ryule5158/A-Rack-for-Eurorack-Modules/exports/Rack4Modules_DesktopTilt60_V04_05_Isometric.png

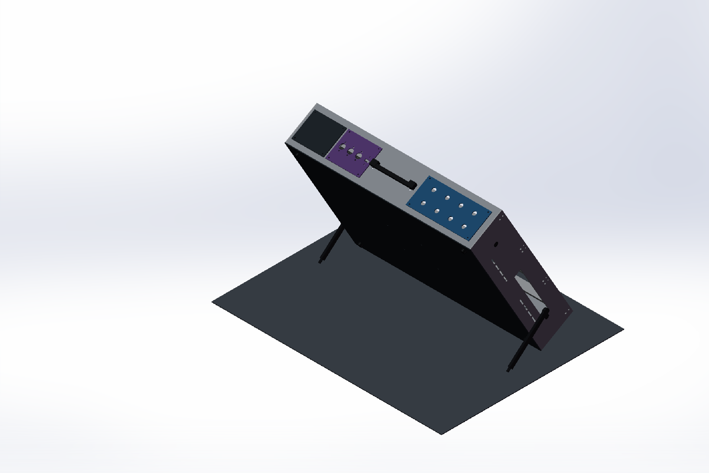
exports/Rack4Modules_DesktopTilt60_V04_05_Isometric.png
