ryule5158/A-Rack-for-Eurorack-Modules/exports/Rack4Modules_OpenCase_V04_01_ModuleFront.png

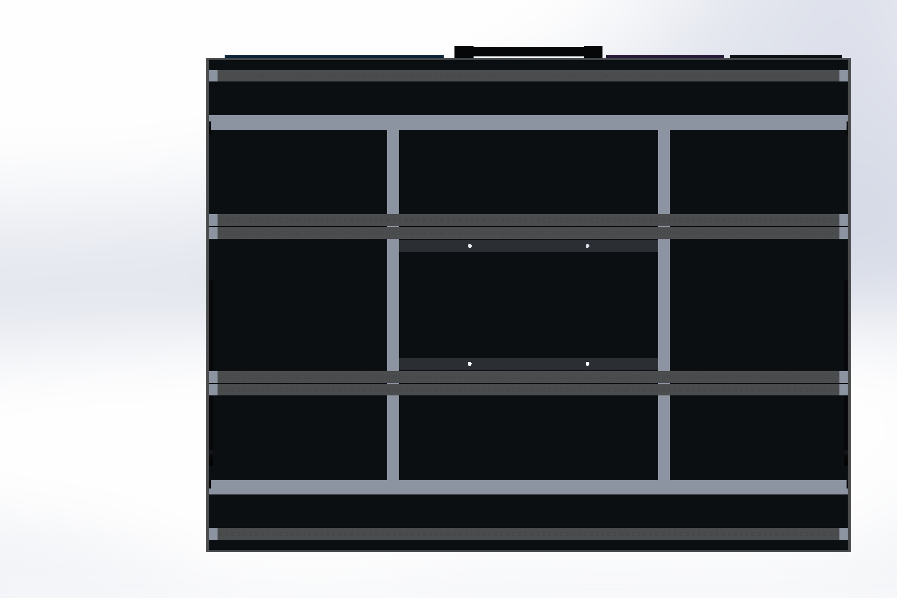
exports/Rack4Modules_OpenCase_V04_01_ModuleFront.png
