ryule5158/A-Rack-for-Eurorack-Modules/exports/Rack4Modules_OpenCase_V04_02_Isometric.png

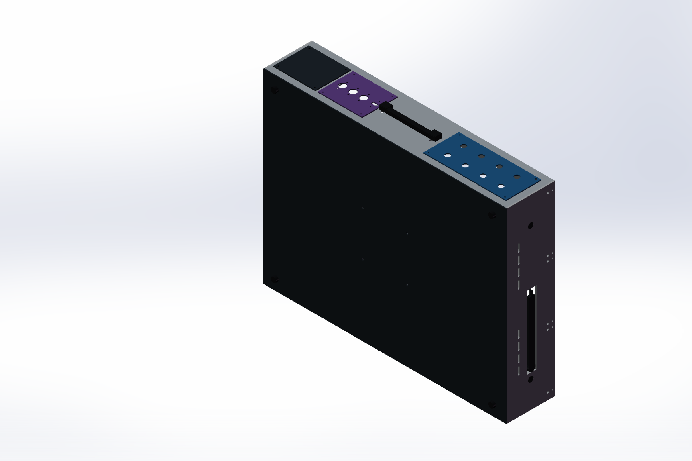
exports/Rack4Modules_OpenCase_V04_02_Isometric.png
