ryule5158/A-Rack-for-Eurorack-Modules/exports/Rack4Modules_OpenCase_V04_03_UpperEdge_IO.png

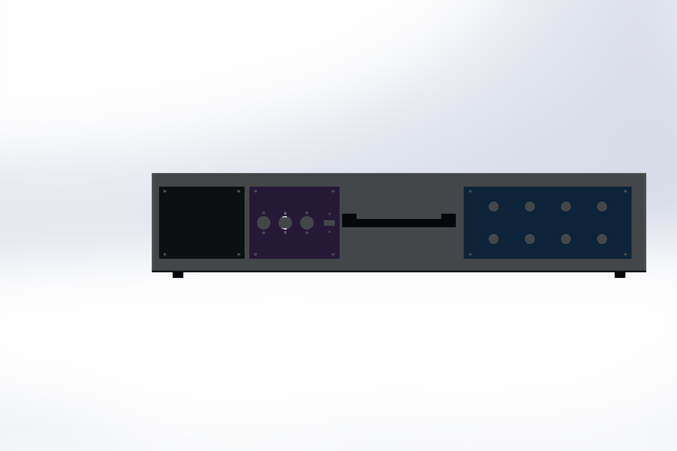
exports/Rack4Modules_OpenCase_V04_03_UpperEdge_IO.png
