ryule5158/A-Rack-for-Eurorack-Modules/previews/Rack4Modules_DesktopTilt60_07_Isometric_V07.png

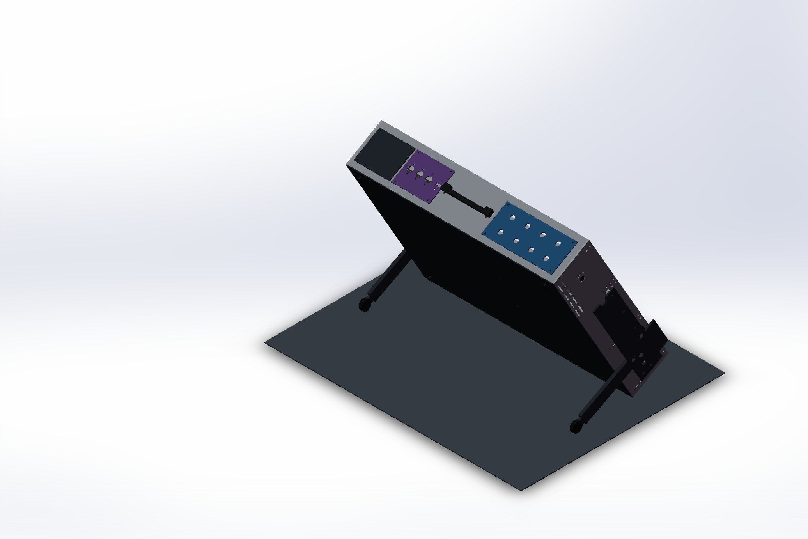
previews/Rack4Modules_DesktopTilt60_07_Isometric_V07.png
