ryule5158/A-Rack-for-Eurorack-Modules/previews/Rack4Modules_ShowcaseTilt60_LidOff_01_Isometric_V07.png

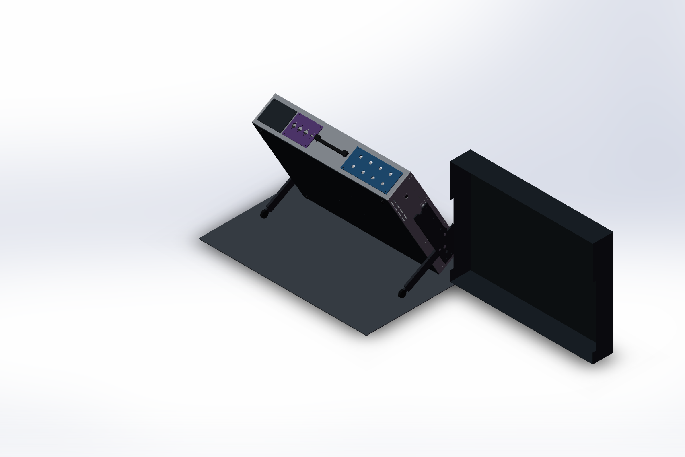
previews/Rack4Modules_ShowcaseTilt60_LidOff_01_Isometric_V07.png
