ryule5158/A-Rack-for-Eurorack-Modules/previews/Rack4Modules_TransportClosed_06_RightSide_V07.png

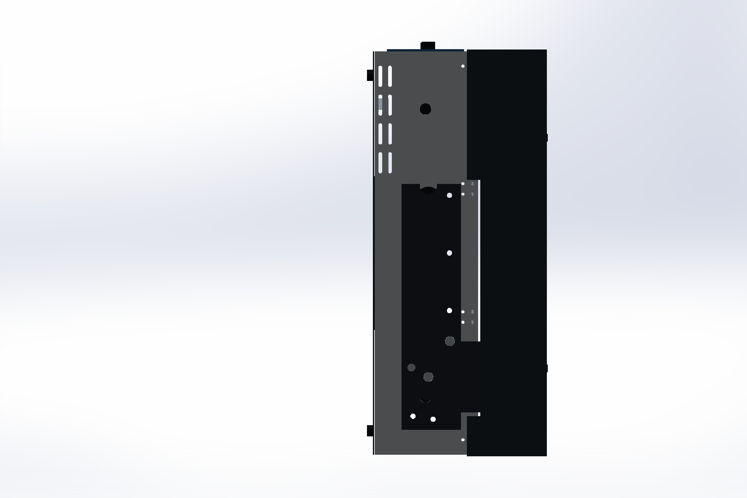
previews/Rack4Modules_TransportClosed_06_RightSide_V07.png
