ryule5158/A-Rack-for-Eurorack-Modules/exports/StandOuterCheek_V11_4mm_FullPlate.STEP

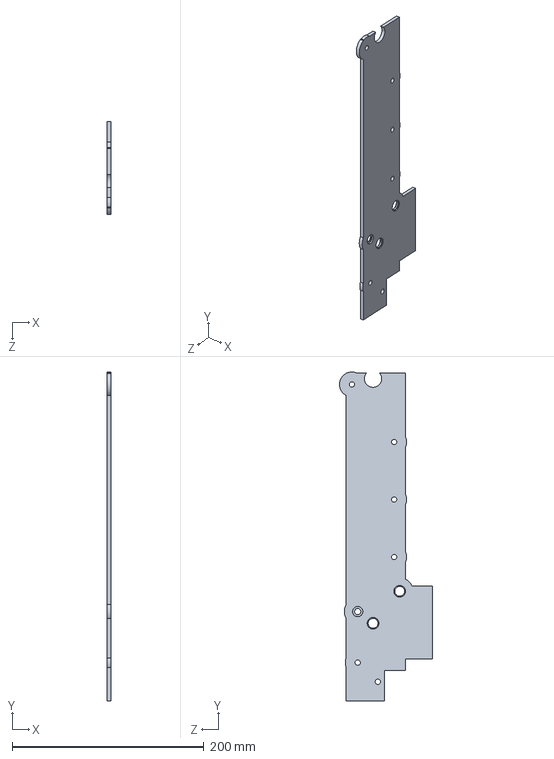
[picture p13: CAD file, 2026-08-29]
exports/StandOuterCheek_V11_4mm_FullPlate.STEP
4.00 x 343.0 x 97.0 mm
