ryule5158/A-Rack-for-Eurorack-Modules/cad/parts/DeepTravelLid_V08_Rymovia_StandRelief.SLDPRT

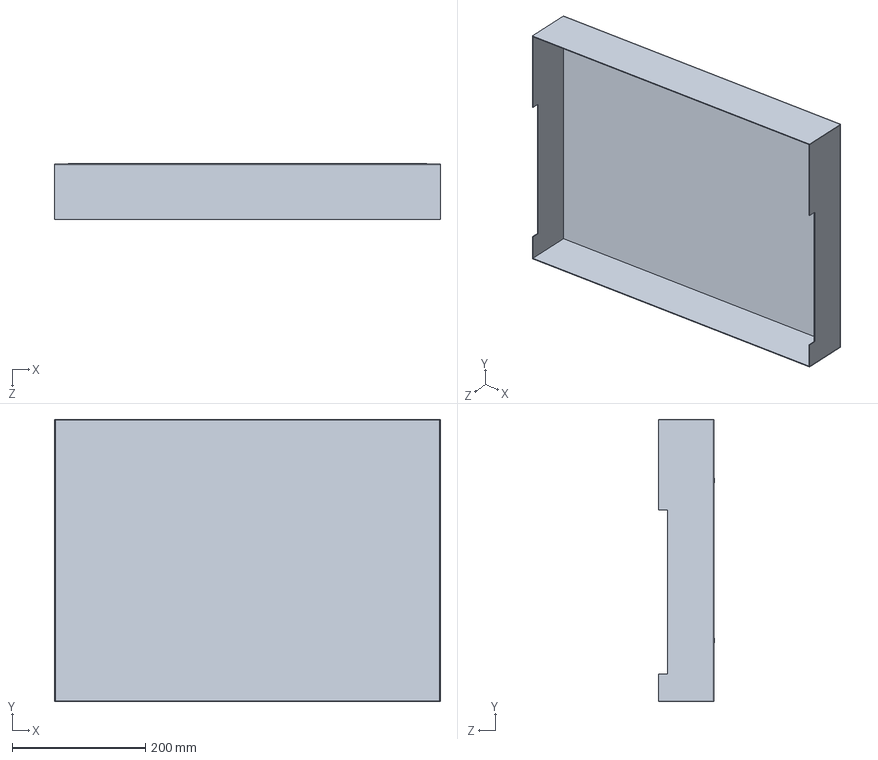
[picture p14: CAD file, 2026-08-26]
cad/parts/DeepTravelLid_V08_Rymovia_StandRelief.SLDPRT
579.0 x 423.4 x 84.4 mm
