ryule5158/A-Rack-for-Eurorack-Modules/exports/RearKickstandHeelPin_V11_M4.STEP

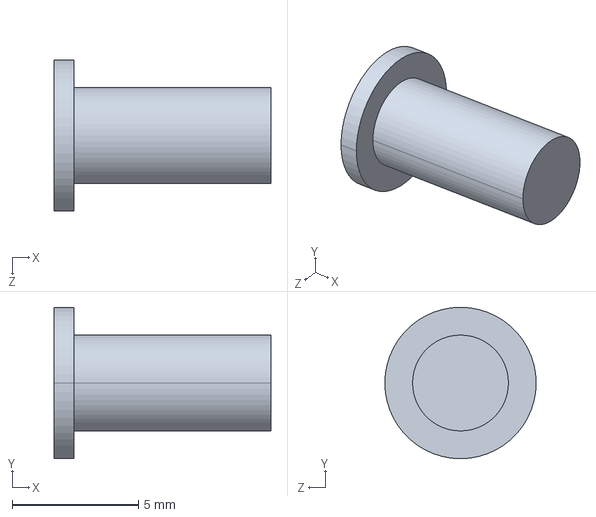
[picture p15: CAD file, 2026-08-29]
exports/RearKickstandHeelPin_V11_M4.STEP
8.60 x 6.00 x 6.00 mm
