ryule5158/A-Rack-for-Eurorack-Modules/cad/parts/RailEndBlock_M3.SLDPRT

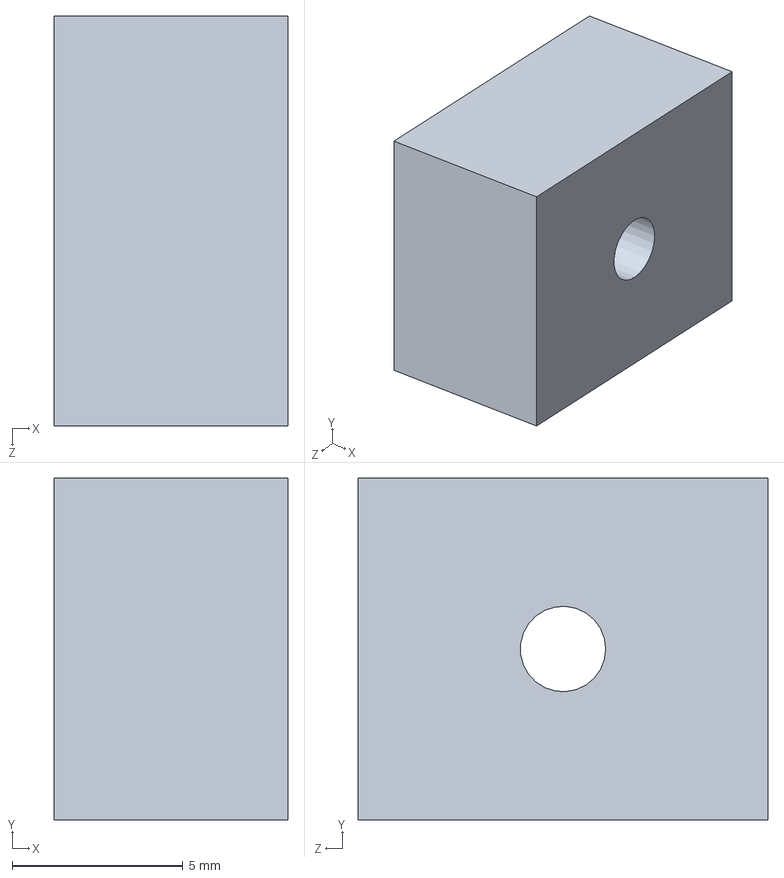
[picture p16: CAD file, 2026-08-26]
cad/parts/RailEndBlock_M3.SLDPRT
6.84 x 10.0 x 12.0 mm
