ryule5158/A-Rack-for-Eurorack-Modules/cad/parts/SideRecessedLeg_V03_TwoPosition.SLDPRT

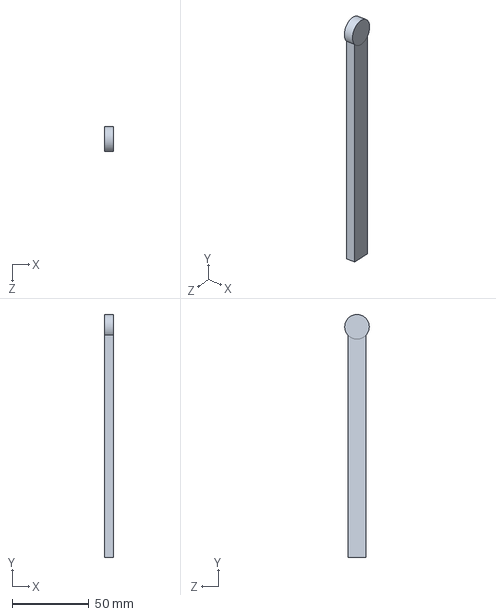
[picture p18: CAD file, 2026-08-26]
cad/parts/SideRecessedLeg_V03_TwoPosition.SLDPRT
6.00 x 158.0 x 16.0 mm
