ryule5158/A-Rack-for-Eurorack-Modules/exports/StandCheekFastenerPack_V11_M5.STEP

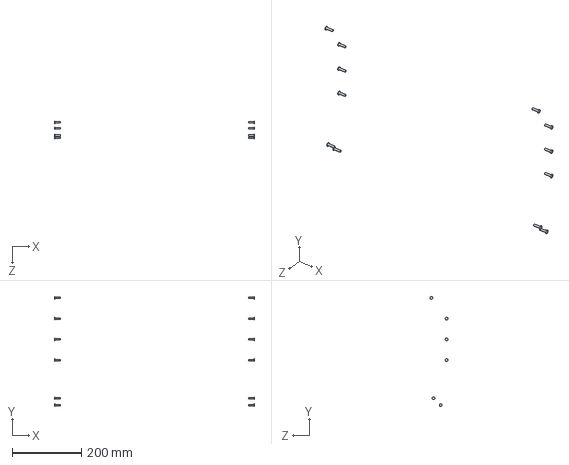
[picture p19: CAD file, 2026-08-29]
exports/StandCheekFastenerPack_V11_M5.STEP
577.6 x 318.5 x 52.5 mm
