ryule5158/A-Rack-for-Eurorack-Modules/cad/parts/ModuleDepthEnvelope_85mm_V03.SLDPRT

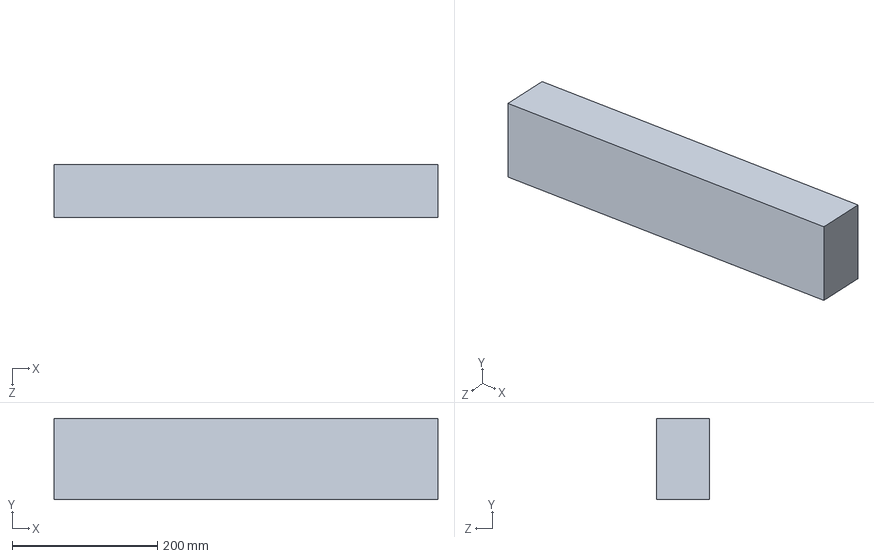
[picture p20: CAD file, 2026-08-26]
cad/parts/ModuleDepthEnvelope_85mm_V03.SLDPRT
528.0 x 112.0 x 73.0 mm
