ryule5158/A-Rack-for-Eurorack-Modules/exports/CarryHandleFastenerPack_V11_2xM4.STEP

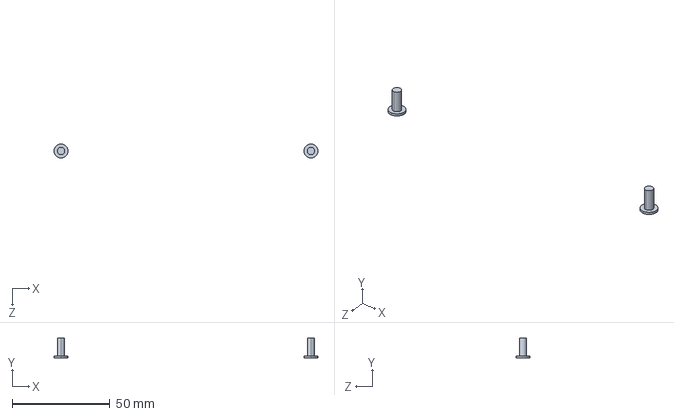
[picture p21: CAD file, 2026-08-29]
exports/CarryHandleFastenerPack_V11_2xM4.STEP
135.2 x 10.0 x 7.20 mm
