ryule5158/A-Rack-for-Eurorack-Modules/cad/parts/EightRubberFeet_Envelope.SLDPRT

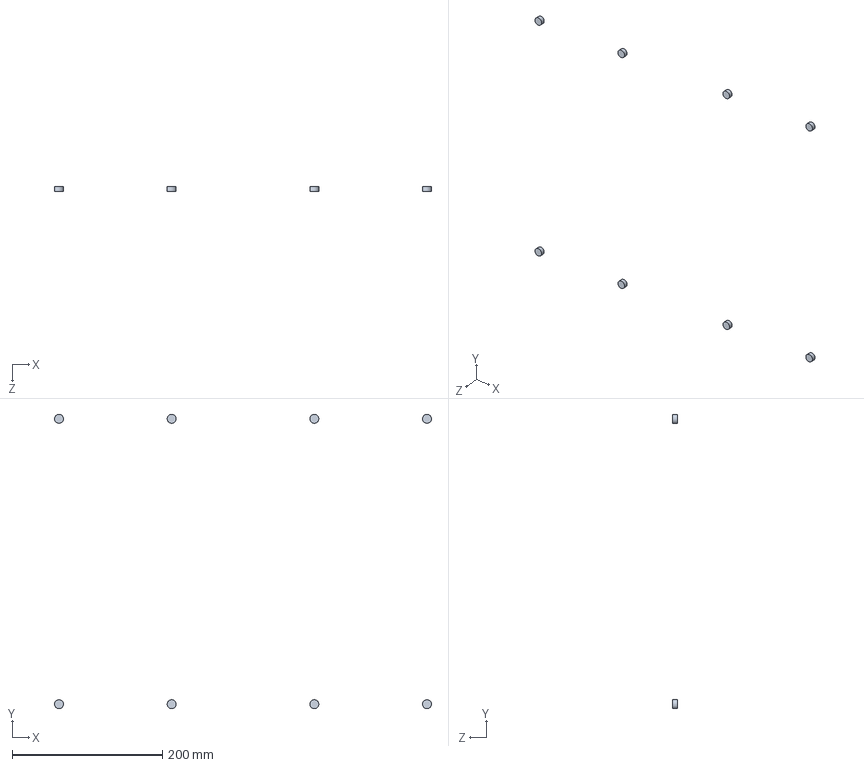
[picture p22: CAD file, 2026-08-26]
cad/parts/EightRubberFeet_Envelope.SLDPRT
502.0 x 392.0 x 6.00 mm
