ryule5158/A-Rack-for-Eurorack-Modules/exports/BackFeetFastenerPack_V11_4xM4.STEP

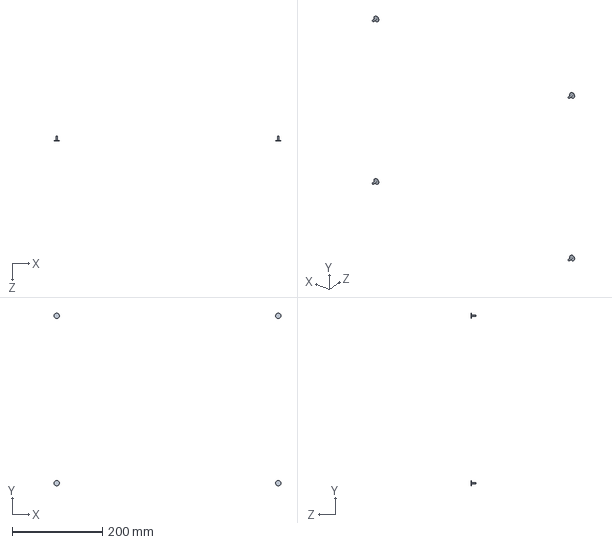
[picture p23: CAD file, 2026-08-29]
exports/BackFeetFastenerPack_V11_4xM4.STEP
502.0 x 382.0 x 11.2 mm
