ryule5158/A-Rack-for-Eurorack-Modules/cad/parts/FoldOutLeg_Concept.SLDPRT

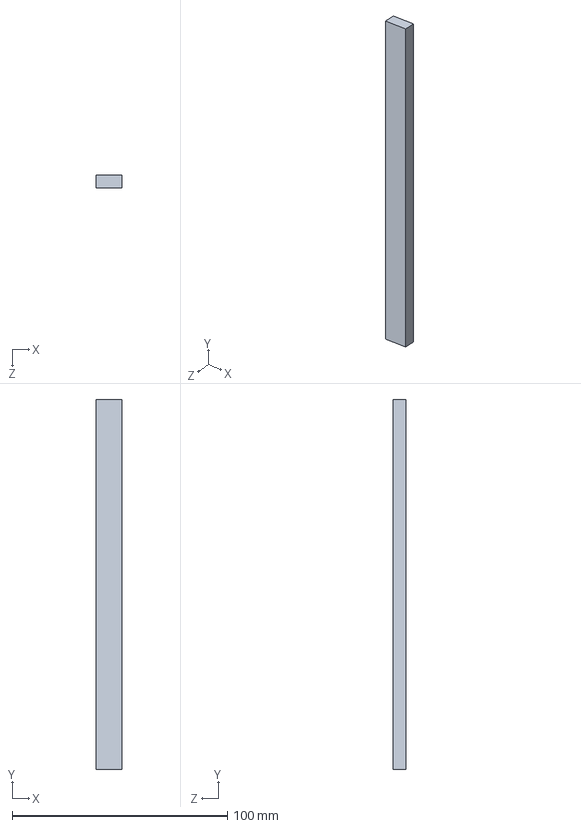
[picture p24: CAD file, 2026-08-26]
cad/parts/FoldOutLeg_Concept.SLDPRT
12.0 x 172.0 x 6.00 mm
