ryule5158/A-Rack-for-Eurorack-Modules/exports/LidCompressionStopPack_V11_EPDM_MetalStop.STEP

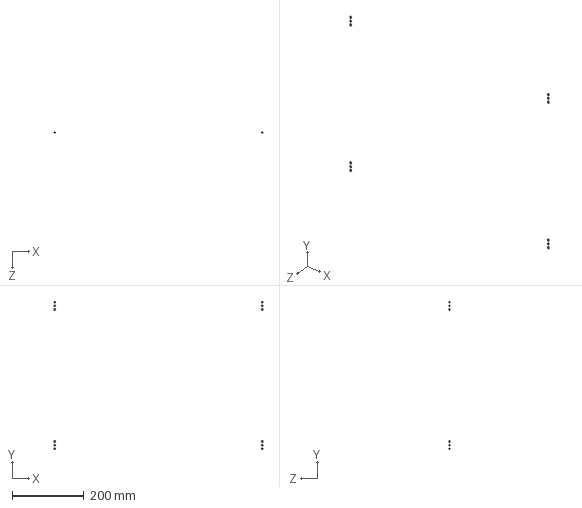
[picture p25: CAD file, 2026-08-29]
exports/LidCompressionStopPack_V11_EPDM_MetalStop.STEP
582.6 x 413.0 x 2.00 mm
