ryule5158/A-Rack-for-Eurorack-Modules/cad/parts/RearCrossBeam_6061.SLDPRT

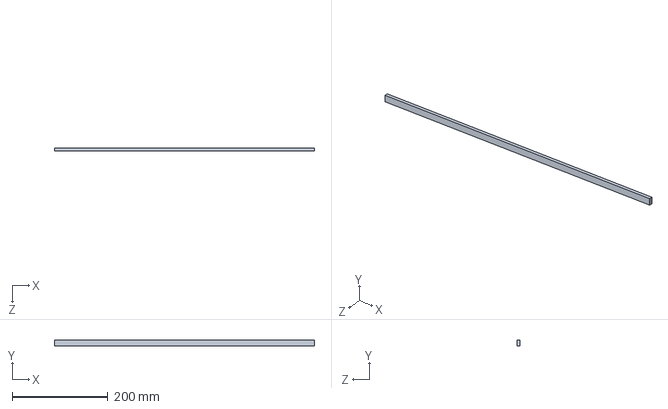
[picture p26: CAD file, 2026-08-26]
cad/parts/RearCrossBeam_6061.SLDPRT
542.0 x 12.0 x 6.00 mm
