ryule5158/A-Rack-for-Eurorack-Modules/exports/BackSkin_V11_5052_RymoviaPhaseHalo.STEP

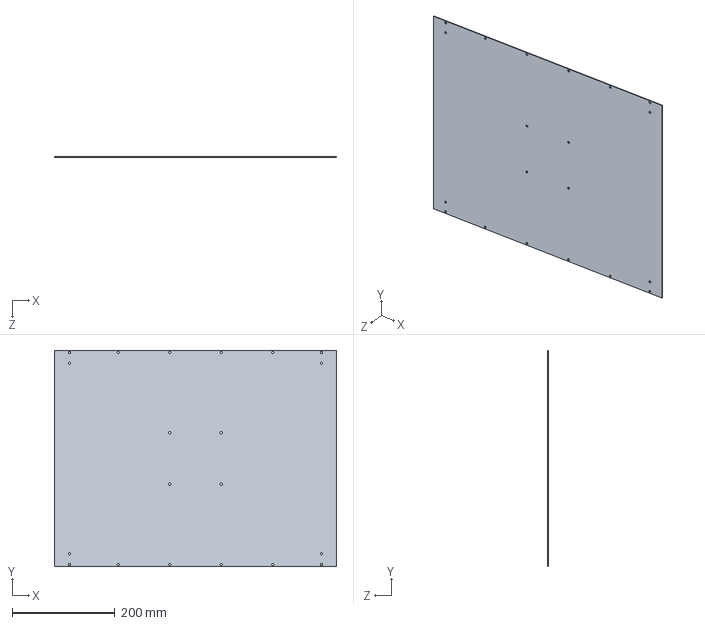
[picture p27: CAD file, 2026-08-29]
exports/BackSkin_V11_5052_RymoviaPhaseHalo.STEP
548.0 x 420.0 x 1.50 mm
