ryule5158/A-Rack-for-Eurorack-Modules/cad/parts/ReservedPowerBus_500x85x20.SLDPRT

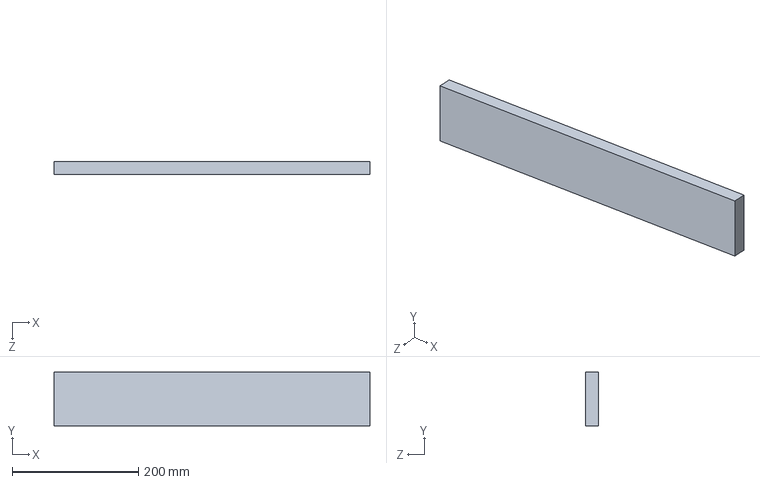
[picture p28: CAD file, 2026-08-26]
cad/parts/ReservedPowerBus_500x85x20.SLDPRT
500.0 x 85.0 x 20.0 mm
