ryule5158/A-Rack-for-Eurorack-Modules/exports/LidLatchCasePack_V11_SouthcoV7.STEP

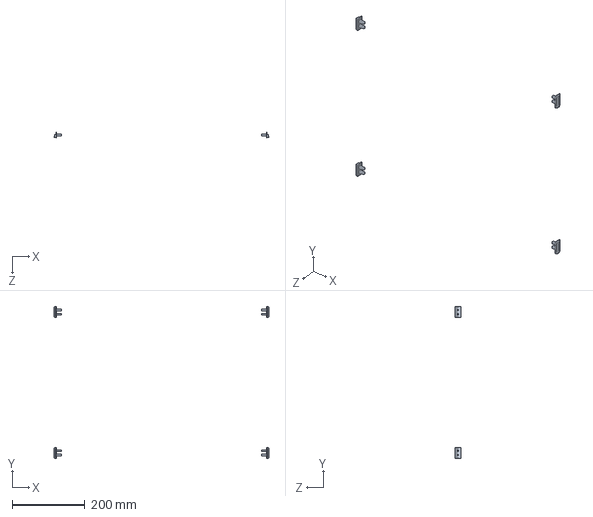
[picture p29: CAD file, 2026-08-29]
exports/LidLatchCasePack_V11_SouthcoV7.STEP
592.0 x 419.0 x 16.0 mm
