ryule5158/A-Rack-for-Eurorack-Modules/cad/parts/FitGauge_104HP_3U.SLDPRT

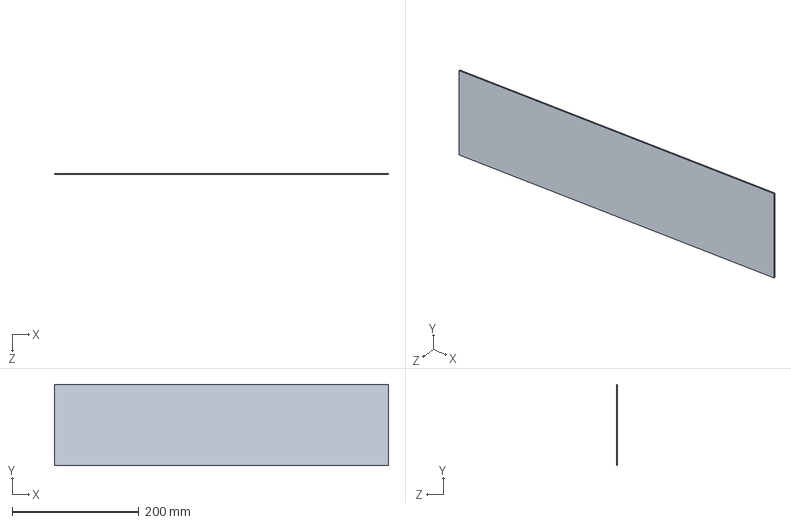
[picture p30: CAD file, 2026-08-26]
cad/parts/FitGauge_104HP_3U.SLDPRT
528.0 x 128.5 x 2.00 mm
