ryule5158/A-Rack-for-Eurorack-Modules/exports/VesaFastenerPack_V11_4xM4_4xSideM4.STEP

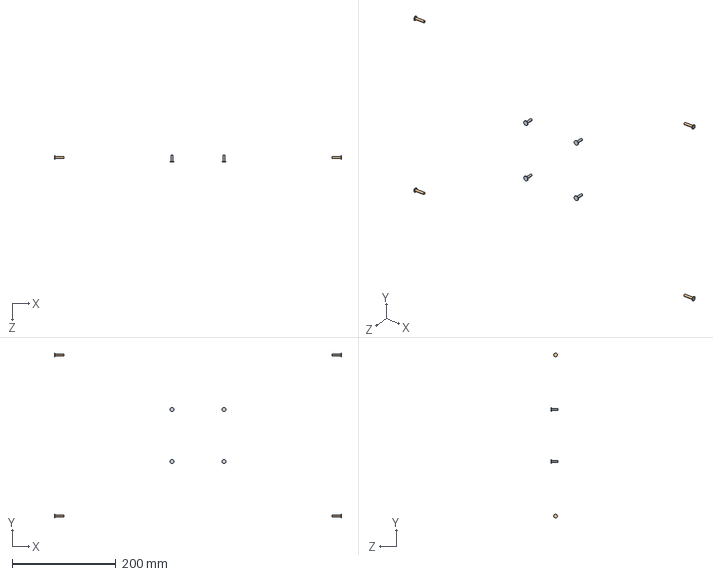
[picture p31: CAD file, 2026-08-29]
exports/VesaFastenerPack_V11_4xM4_4xSideM4.STEP
552.4 x 317.2 x 14.0 mm
