ryule5158/A-Rack-for-Eurorack-Modules/cad/parts/TopFoldFlatHandle_Concept.SLDPRT

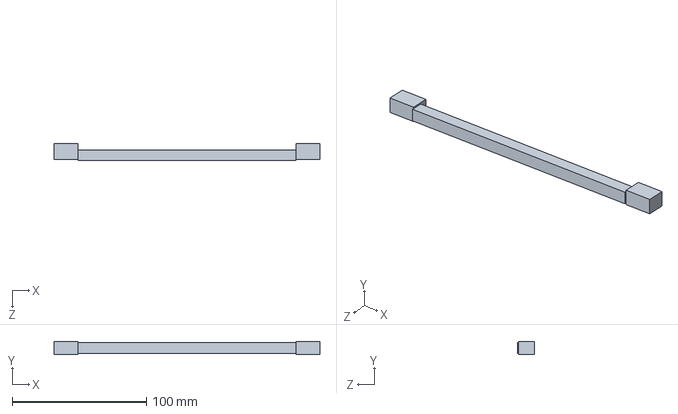
[picture p32: CAD file, 2026-08-26]
cad/parts/TopFoldFlatHandle_Concept.SLDPRT
198.0 x 10.0 x 13.0 mm
