ryule5158/A-Rack-for-Eurorack-Modules/exports/RymoviaRailFastenerPack_V11_12xM3_12xM4.STEP

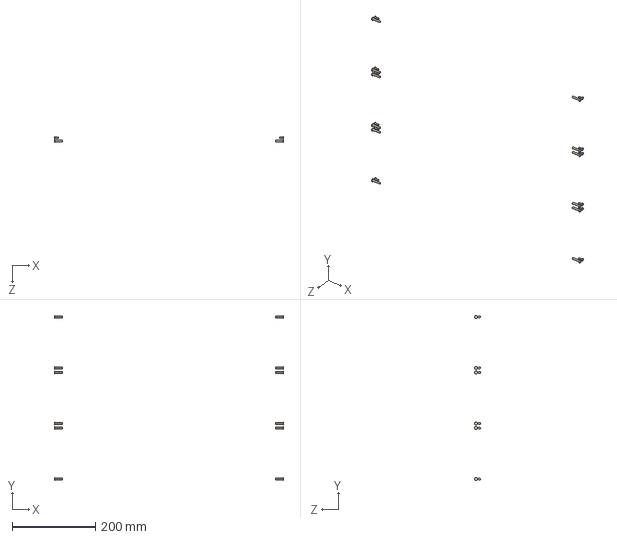
[picture p33: CAD file, 2026-08-29]
exports/RymoviaRailFastenerPack_V11_12xM3_12xM4.STEP
550.0 x 396.4 x 14.5 mm
