ryule5158/A-Rack-for-Eurorack-Modules/cad/parts/LidLatch_Concept.SLDPRT

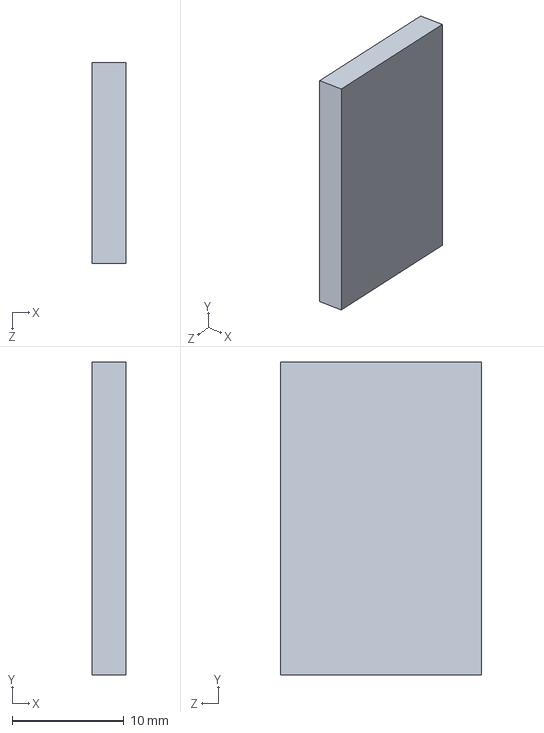
[picture p34: CAD file, 2026-08-26]
cad/parts/LidLatch_Concept.SLDPRT
3.00 x 28.0 x 18.0 mm
