ryule5158/A-Rack-for-Eurorack-Modules/exports/CarryHandleSpreader_V11_P9_128.STEP

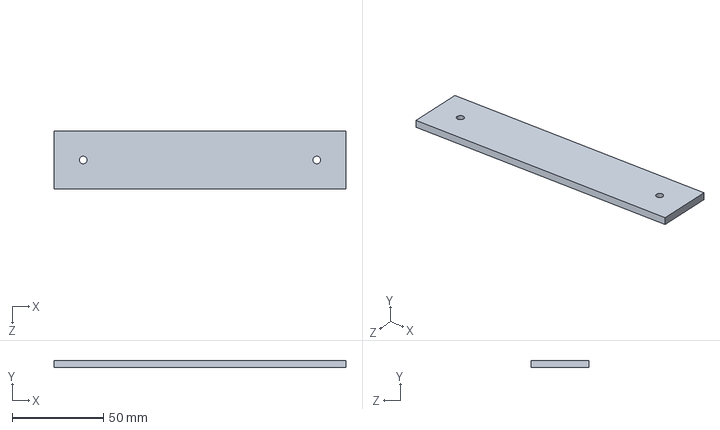
[picture p35: CAD file, 2026-08-29]
exports/CarryHandleSpreader_V11_P9_128.STEP
160.0 x 4.00 x 32.0 mm
