ryule5158/A-Rack-for-Eurorack-Modules/cad/parts/InternalLidCatch_V03.SLDPRT

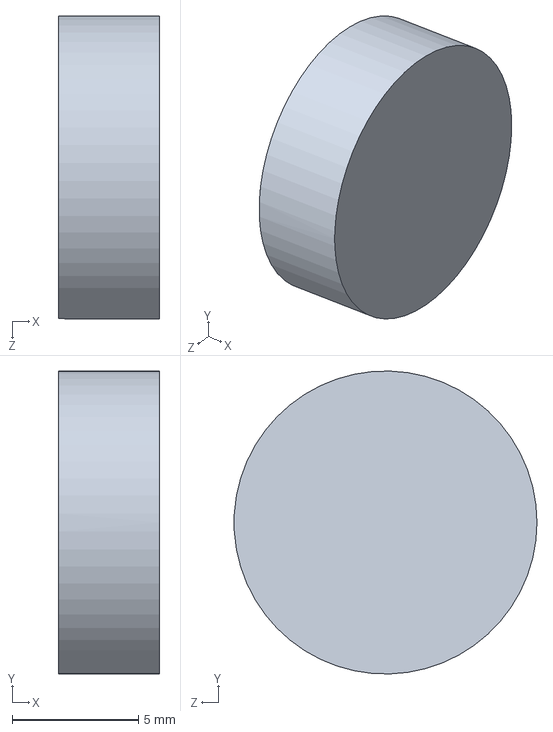
[picture p36: CAD file, 2026-08-26]
cad/parts/InternalLidCatch_V03.SLDPRT
4.00 x 12.0 x 12.0 mm
