ryule5158/A-Rack-for-Eurorack-Modules/exports/RearKickstandBushing_V11_G1SM_1012_08.STEP

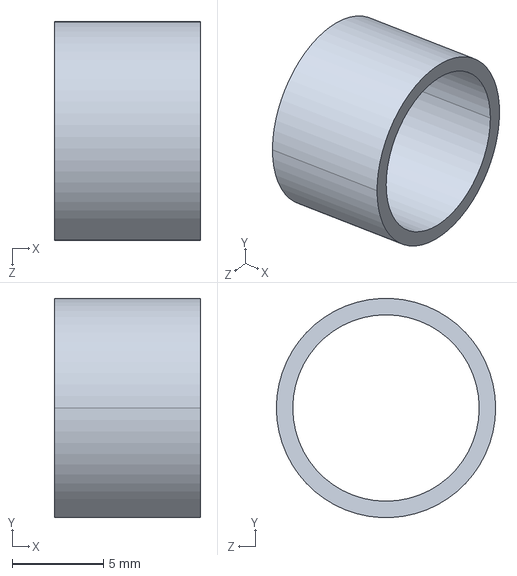
[picture p37: CAD file, 2026-08-29]
exports/RearKickstandBushing_V11_G1SM_1012_08.STEP
8.00 x 12.0 x 12.0 mm
