ryule5158/A-Rack-for-Eurorack-Modules/cad/parts/DesktopReferenceSurface_V04.SLDPRT

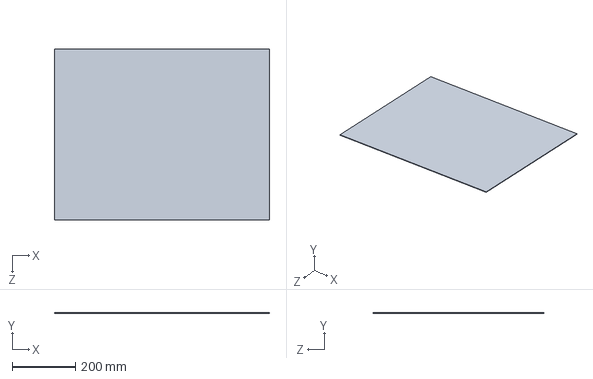
[picture p39: CAD file, 2026-08-26]
cad/parts/DesktopReferenceSurface_V04.SLDPRT
680.0 x 2.00 x 540.0 mm
