ryule5158/A-Rack-for-Eurorack-Modules/cad/parts/FourBackFeet_V03.SLDPRT

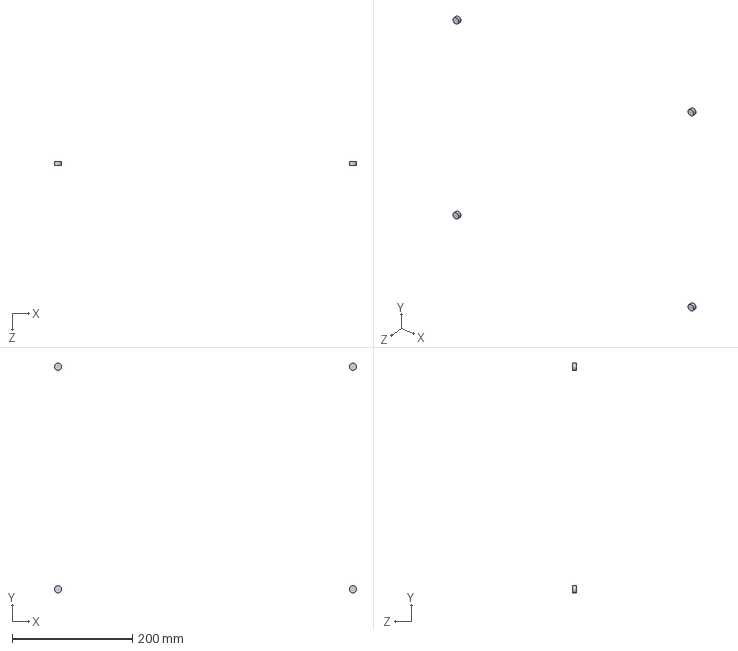
[picture p41: CAD file, 2026-08-26]
cad/parts/FourBackFeet_V03.SLDPRT
502.0 x 382.0 x 6.00 mm
