ryule5158/A-Rack-for-Eurorack-Modules/cad/parts/VesaBridge_6061.SLDPRT

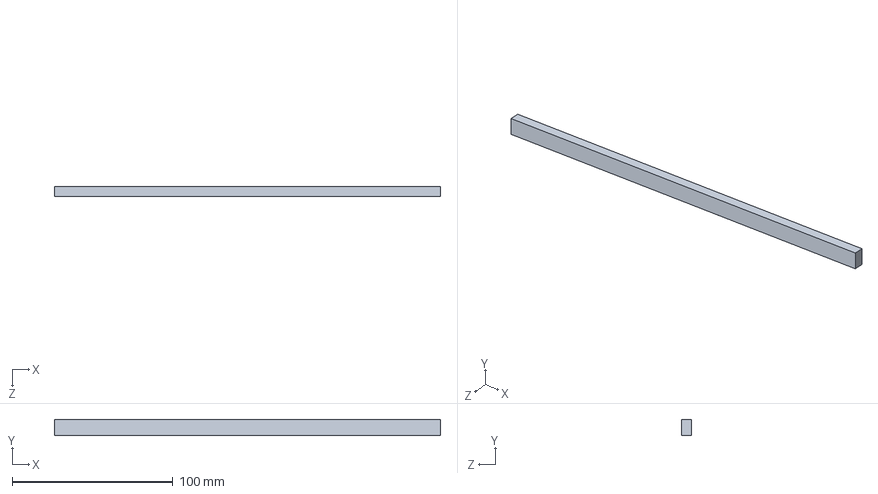
[picture p43: CAD file, 2026-08-26]
cad/parts/VesaBridge_6061.SLDPRT
240.0 x 10.0 x 6.00 mm
