ryule5158/A-Rack-for-Eurorack-Modules/exports/LidLatchFastenerPack_V11_16xM3.STEP

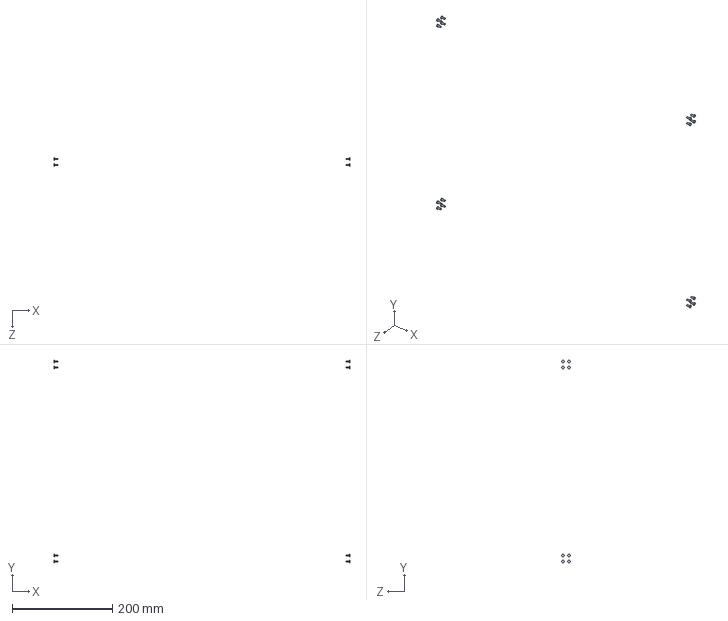
[picture p44: CAD file, 2026-08-29]
exports/LidLatchFastenerPack_V11_16xM3.STEP
591.8 x 405.5 x 17.5 mm
