ryule5158/A-Rack-for-Eurorack-Modules/cad/parts/VesaStile_6061.SLDPRT

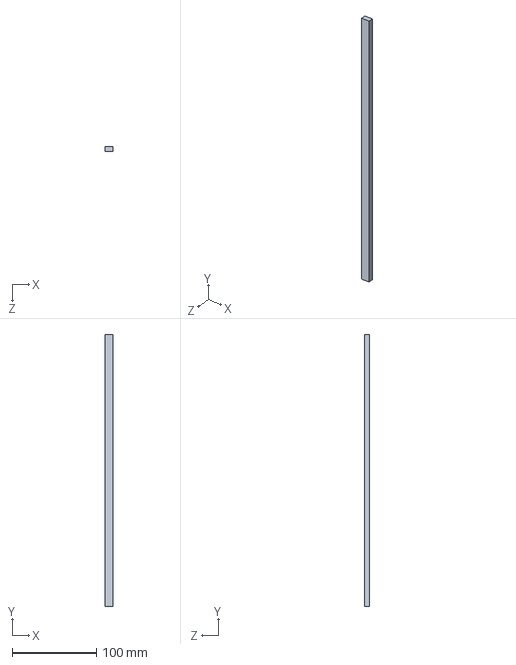
[picture p46: CAD file, 2026-08-26]
cad/parts/VesaStile_6061.SLDPRT
10.0 x 322.0 x 6.00 mm
