ryule5158/A-Rack-for-Eurorack-Modules/exports/RearKickstandPivotAxle_V11_Retained10mm.STEP

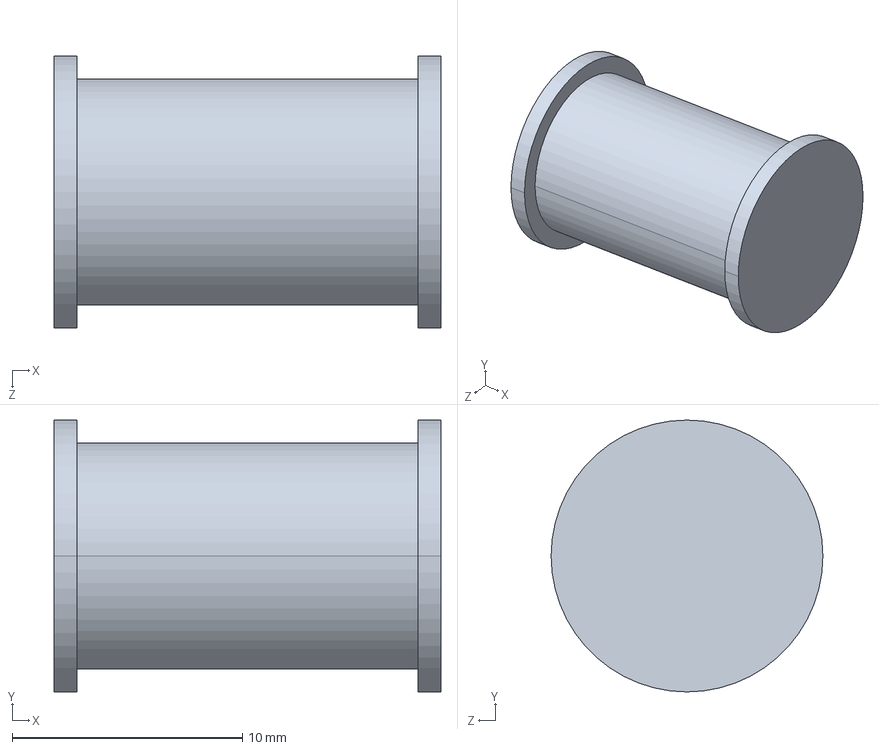
[picture p47: CAD file, 2026-08-29]
exports/RearKickstandPivotAxle_V11_Retained10mm.STEP
16.8 x 11.8 x 11.8 mm
