ryule5158/A-Rack-for-Eurorack-Modules/cad/parts/RearCarryHandle_V03_Reference.SLDPRT

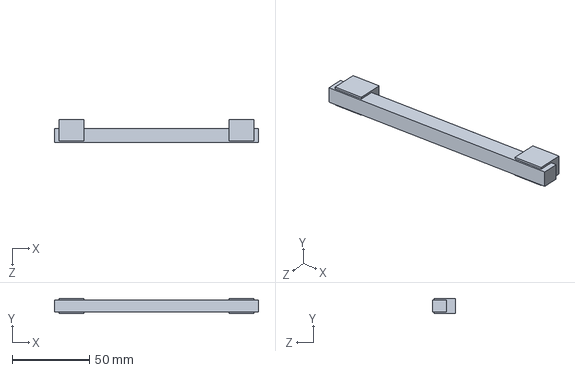
[picture p48: CAD file, 2026-08-26]
cad/parts/RearCarryHandle_V03_Reference.SLDPRT
132.0 x 10.0 x 15.0 mm
