ryule5158/A-Rack-for-Eurorack-Modules/exports/RymoviaRail_104HP_V11_ClosedTubeDualFix.STEP

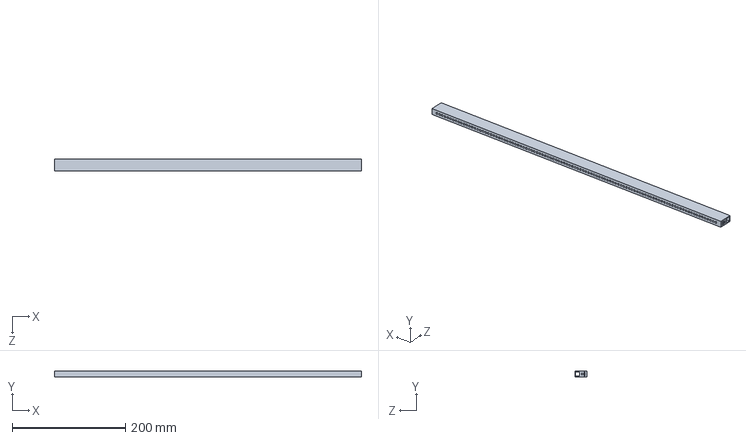
[picture p49: CAD file, 2026-08-29]
exports/RymoviaRail_104HP_V11_ClosedTubeDualFix.STEP
542.0 x 10.0 x 22.0 mm
