ryule5158/A-Rack-for-Eurorack-Modules/cad/parts/ReservedPowerSupply_210x90x45.SLDPRT

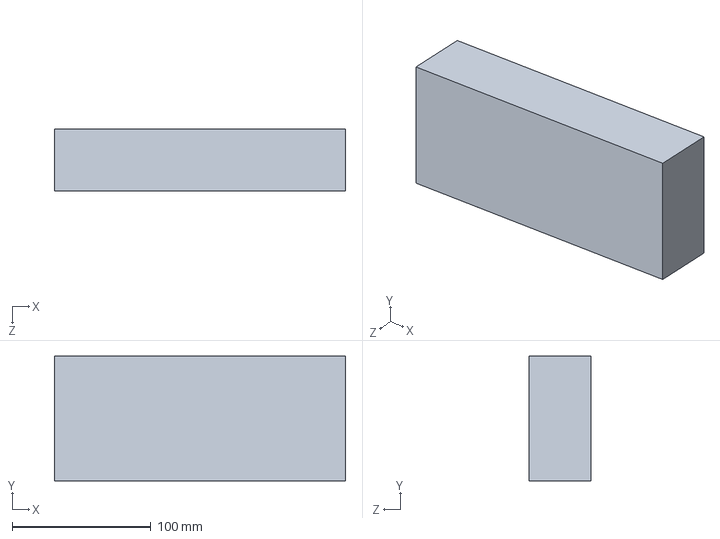
[picture p50: CAD file, 2026-08-26]
cad/parts/ReservedPowerSupply_210x90x45.SLDPRT
210.0 x 90.0 x 45.0 mm
