ryule5158/A-Rack-for-Eurorack-Modules/exports/UpperCassetteFastenerPack_V11_12xM3.STEP

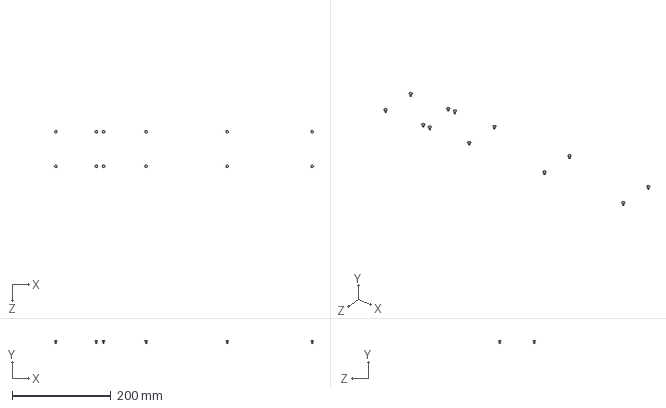
[picture p51: CAD file, 2026-08-29]
exports/UpperCassetteFastenerPack_V11_12xM3.STEP
524.0 x 5.40 x 75.5 mm
