ryule5158/A-Rack-for-Eurorack-Modules/exports/Rack4Modules_ClearanceCheck_V11_MechanicalRelease.STEP

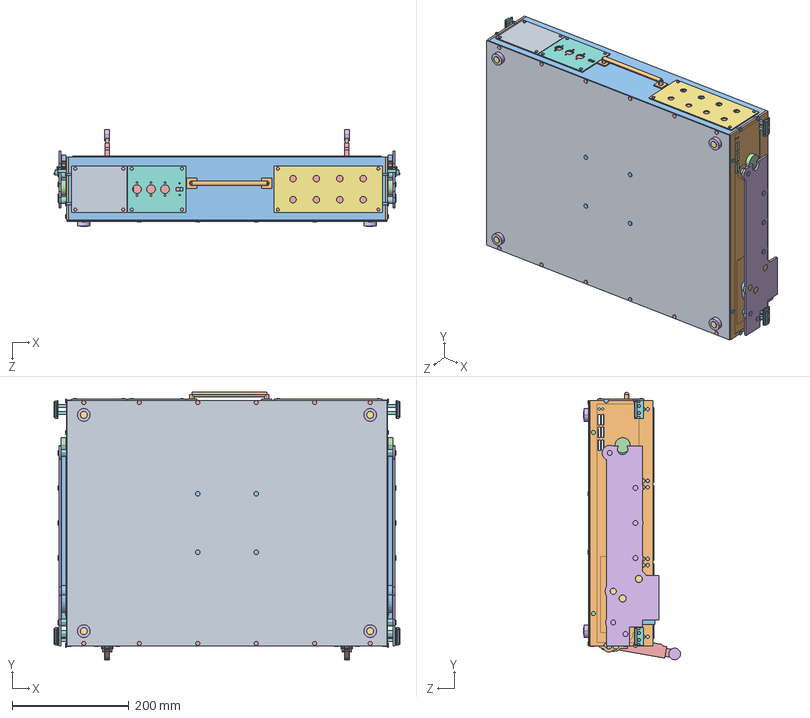
[picture p52: CAD file, 2026-08-29]
exports/Rack4Modules_ClearanceCheck_V11_MechanicalRelease.STEP
592.0 x 457.8 x 166.1 mm
BackSkin_V11_5052_RymoviaPhaseHalo
SideFrame_V11_ReleaseDoubleShear x 2
UpperEdge_V11_P9_Handle_ShellJoints
LowerEdge_V11_Vented_AntiTipMounts
RymoviaRail_104HP_V11_ClosedTubeDualFix x 6
RymoviaRail_104HP_V11_AISI304_ThreadStrip x 6
UpperAudio_V04_2x4_TRS635
UpperMidiUsb_V04_3xDIN_USB_C_Inline
UpperAdapterBlank_V04_95mm
CarryHandle_V11_SouthcoP9_128
RearKickstand_V11_262mm_Bushed x 2
FitGauge_104HP_3U x 3
ModuleDepthEnvelope_85mm_V03 x 3
ReservedPowerBus_500x85x20
ReservedPowerSupply_210x90x45
CarryHandleSpreader_V11_P9_128
BackVesaDoubler_V11_5052_Separate
VesaLoadFrame_V11_OnePiece6061
VesaFastenerPack_V11_4xM4_4xSideM4
BackPerimeterFastenerPack_V11_12xM4
BackFeetPack_V11_4xCapturedEPDM
BackFeetFastenerPack_V11_4xM4
RymoviaRailEndInsertPack_V11_12x7075_M4
RymoviaRailFastenerPack_V11_12xM3_12xM4
ShellCornerFastenerPack_V11_8xM4
CarryHandleFastenerPack_V11_2xM4
UpperCassetteFastenerPack_V11_12xM3
StandCheekFastenerPack_V11_M5
RearKickstandLockScrewPack_V11_M6_FlushCaptive
LidLatchCasePack_V11_SouthcoV7
LidLatchCaseFastenerPack_V11_8xM3
FrontAntiTipBracketPack_V11_DoubleShear
FrontAntiTipPivotPack_V11_Retained8mm
FrontAntiTipStopPack_V11_Retained8mm
FrontAntiTipLockPack_V11_M6_FlushCaptive
FrontAntiTipBracketFastenerPack_V11_8xM4
StandOuterCheek_V11_4mm_FullPlate x 2
RearKickstandPivotAxle_V11_Retained10mm x 2
RearKickstandStopAxle_V11_Retained10mm x 2
StandCheekSpacer_V11_8p8mm_M5 x 12
RearKickstandBushing_V11_G1SM_1012_08 x 2
RearKickstandHeel_V11_17_4PH_Keyed x 2
RearKickstandHeelPin_V11_M4 x 2
RearKickstandFoot_V11_OvermouldCaptured x 2
FrontAntiTipLink_V11_124mm_17_4PH x 2
FrontAntiTipFoot_V11_OvermouldCaptured x 2
