ryule5158/A-Rack-for-Eurorack-Modules/exports/FrontAntiTipStopPack_V11_Retained8mm.STEP

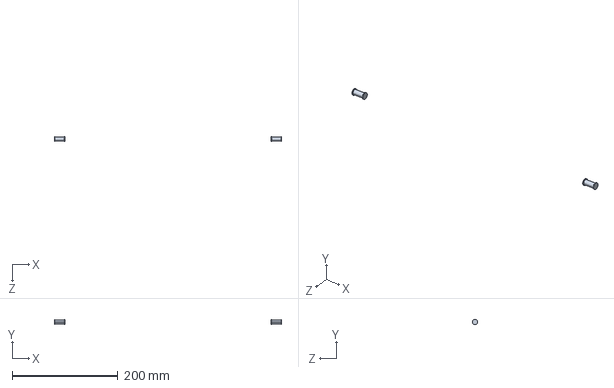
[picture p56: CAD file, 2026-08-29]
exports/FrontAntiTipStopPack_V11_Retained8mm.STEP
429.4 x 10.0 x 10.0 mm
