ryule5158/A-Rack-for-Eurorack-Modules/exports/UpperEdge_V11_P9_Handle_ShellJoints.STEP

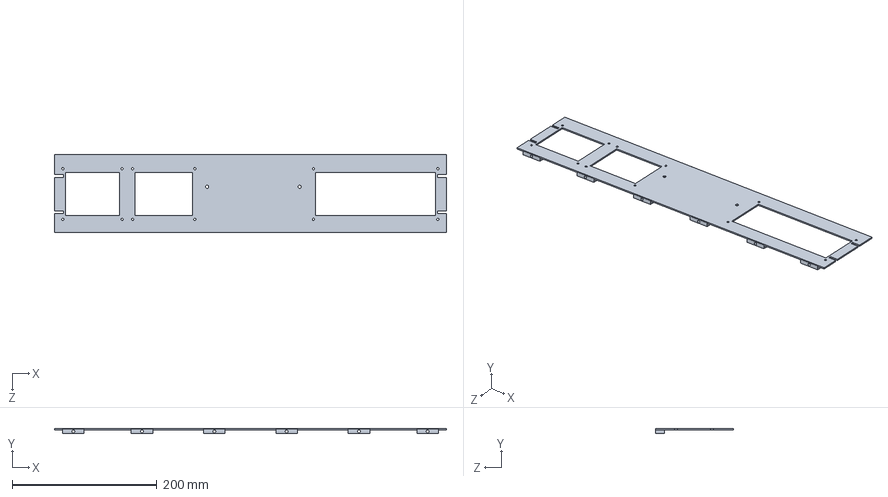
[picture p58: CAD file, 2026-08-29]
exports/UpperEdge_V11_P9_Handle_ShellJoints.STEP
542.0 x 7.00 x 108.5 mm
