ryule5158/A-Rack-for-Eurorack-Modules/exports/RearKickstand_V11_262mm_Bushed.STEP

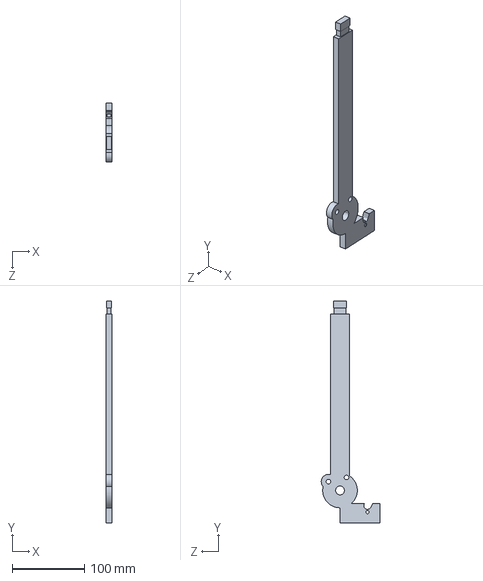
[picture p59: CAD file, 2026-08-29]
exports/RearKickstand_V11_262mm_Bushed.STEP
8.00 x 307.0 x 81.0 mm
