ryule5158/A-Rack-for-Eurorack-Modules/exports/SideFrame_V11_ReleaseDoubleShear.STEP

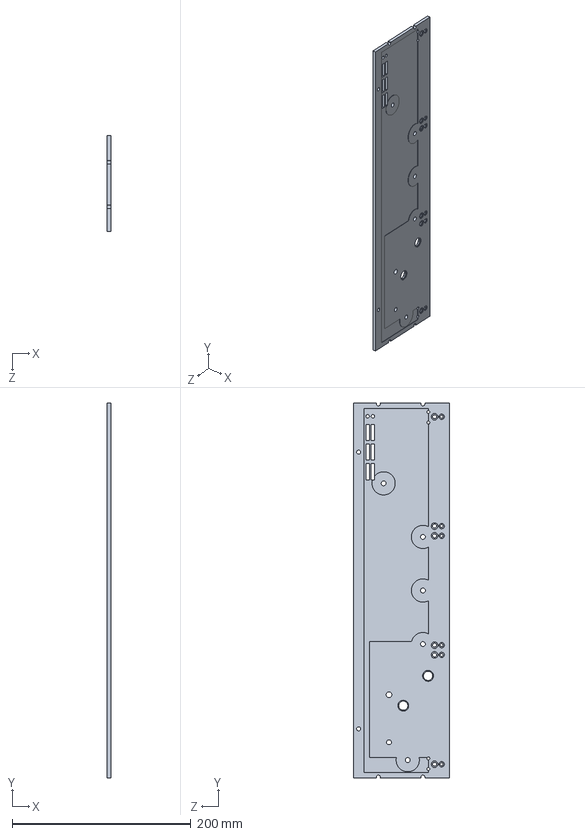
[picture p60: CAD file, 2026-08-29]
exports/SideFrame_V11_ReleaseDoubleShear.STEP
4.00 x 420.0 x 108.0 mm
