ryule5158/A-Rack-for-Eurorack-Modules/exports/FrontAntiTipLink_V11_124mm_17_4PH.STEP

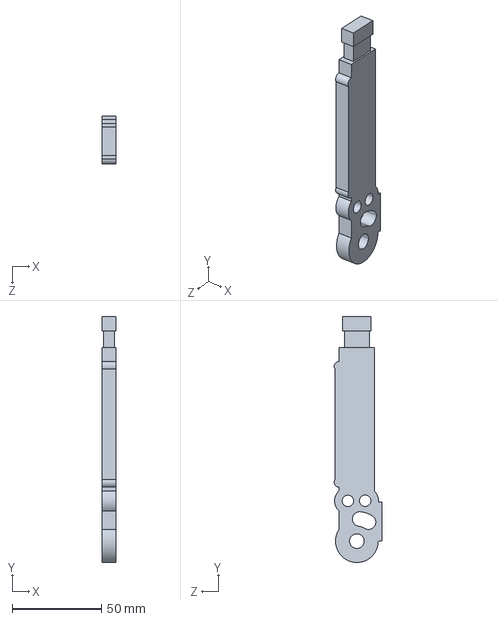
[picture p61: CAD file, 2026-08-29]
exports/FrontAntiTipLink_V11_124mm_17_4PH.STEP
8.00 x 138.0 x 26.7 mm
