ryule5158/A-Rack-for-Eurorack-Modules/exports/LidLatchCaseFastenerPack_V11_8xM3.STEP

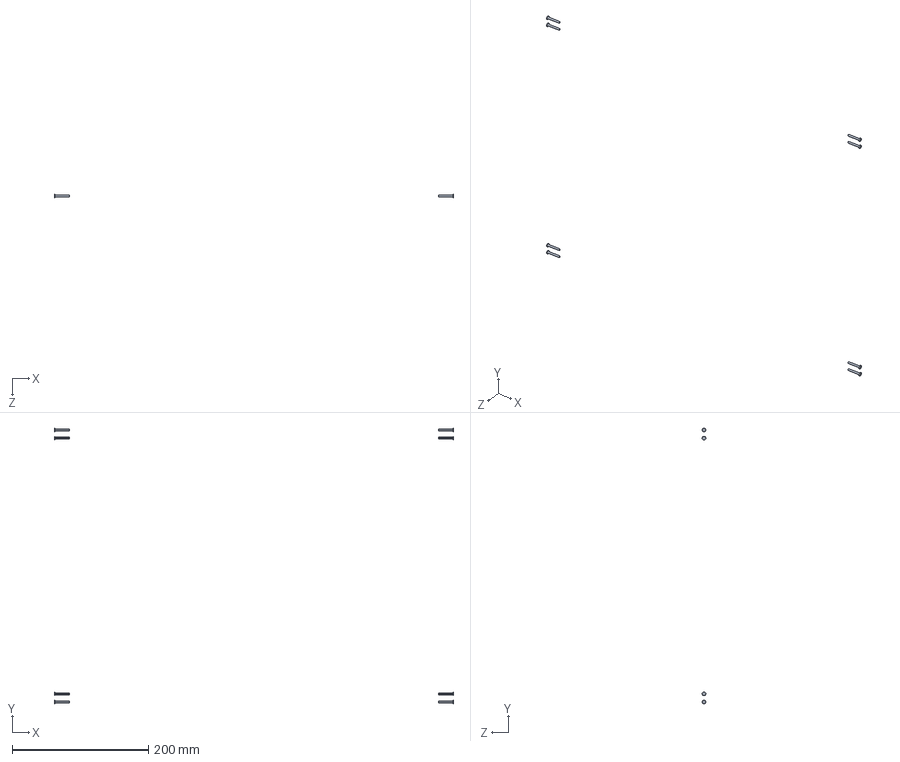
[picture p62: CAD file, 2026-08-29]
exports/LidLatchCaseFastenerPack_V11_8xM3.STEP
586.6 x 405.5 x 5.50 mm
