ryule5158/A-Rack-for-Eurorack-Modules/exports/StandCheekSpacer_V11_8p8mm_M5.STEP

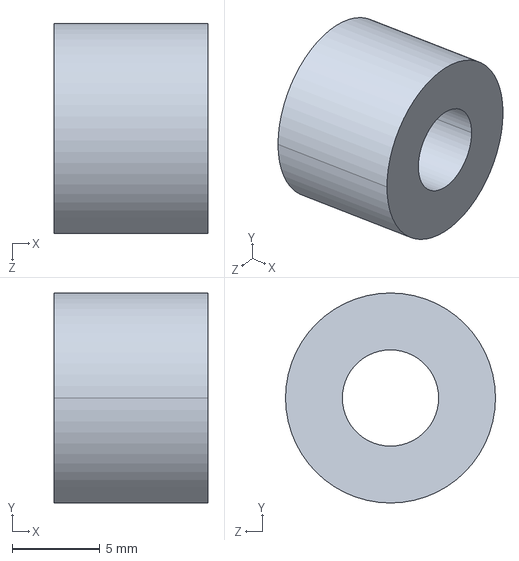
[picture p63: CAD file, 2026-08-29]
exports/StandCheekSpacer_V11_8p8mm_M5.STEP
8.80 x 12.0 x 12.0 mm
