ryule5158/A-Rack-for-Eurorack-Modules/exports/RymoviaRailEndInsertPack_V11_12x7075_M4.STEP

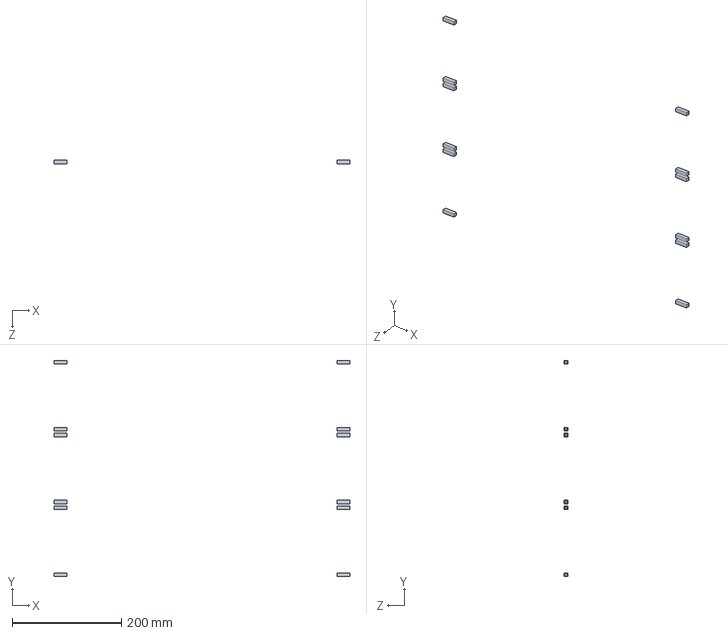
[picture p64: CAD file, 2026-08-29]
exports/RymoviaRailEndInsertPack_V11_12x7075_M4.STEP
541.8 x 396.0 x 6.80 mm
