ryule5158/A-Rack-for-Eurorack-Modules/exports/DeepTravelLid_V11_WeldedContinuous_SouthcoV7.STEP

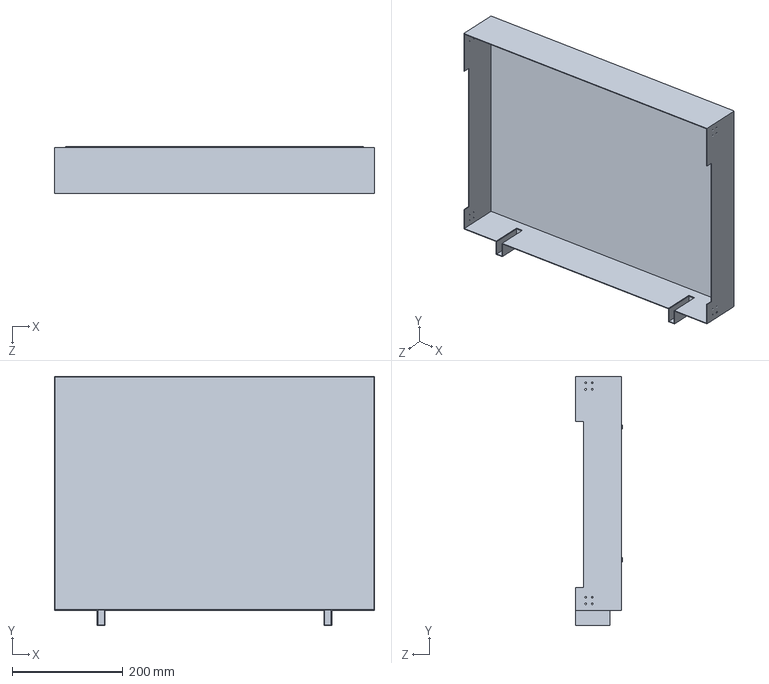
[picture p65: CAD file, 2026-08-29]
exports/DeepTravelLid_V11_WeldedContinuous_SouthcoV7.STEP
579.0 x 451.1 x 84.4 mm
