ryule5158/A-Rack-for-Eurorack-Modules/exports/FrontAntiTipLockPack_V11_M6_FlushCaptive.STEP

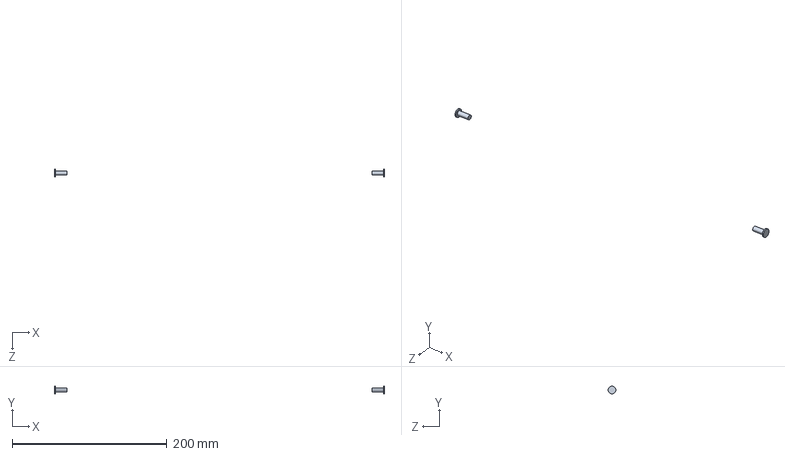
[picture p66: CAD file, 2026-08-29]
exports/FrontAntiTipLockPack_V11_M6_FlushCaptive.STEP
426.4 x 10.0 x 10.0 mm
