ryule5158/A-Rack-for-Eurorack-Modules/exports/BackPerimeterFastenerPack_V11_12xM4.STEP

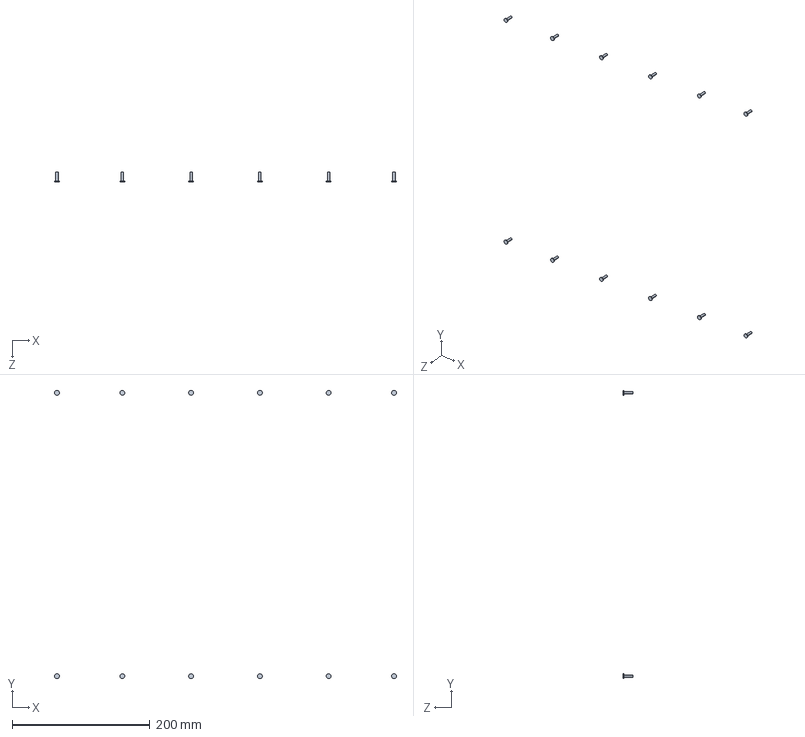
[picture p67: CAD file, 2026-08-29]
exports/BackPerimeterFastenerPack_V11_12xM4.STEP
497.2 x 419.2 x 14.0 mm
