ryule5158/A-Rack-for-Eurorack-Modules/exports/LidLatchDoublerPack_V11_4x5052.STEP

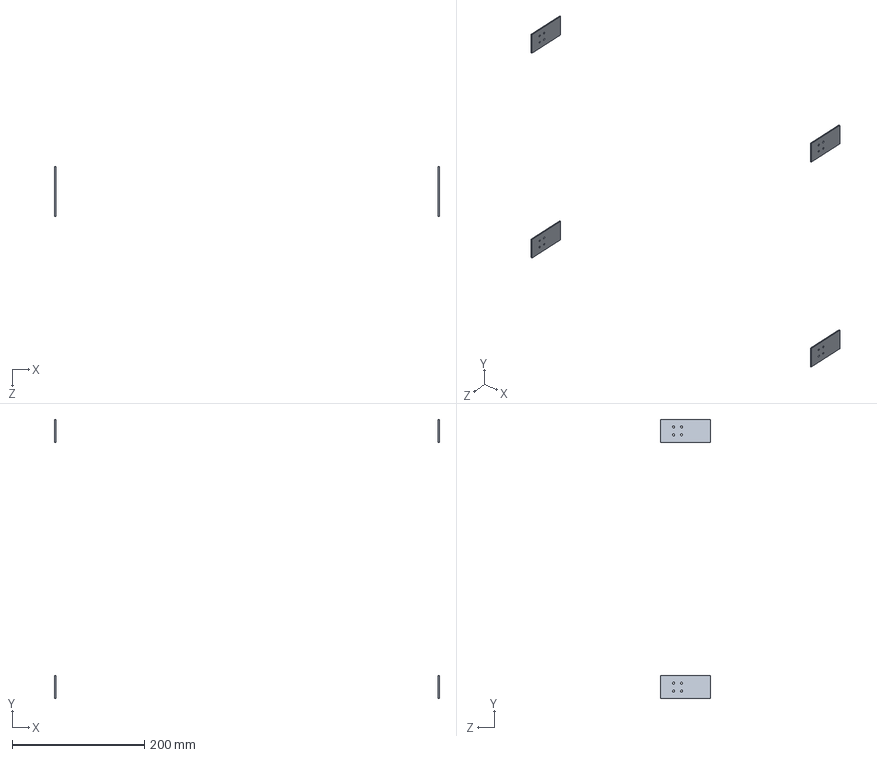
[picture p68: CAD file, 2026-08-29]
exports/LidLatchDoublerPack_V11_4x5052.STEP
583.0 x 423.0 x 76.0 mm
