ryule5158/A-Rack-for-Eurorack-Modules/exports/BackFeetPack_V11_4xCapturedEPDM.STEP

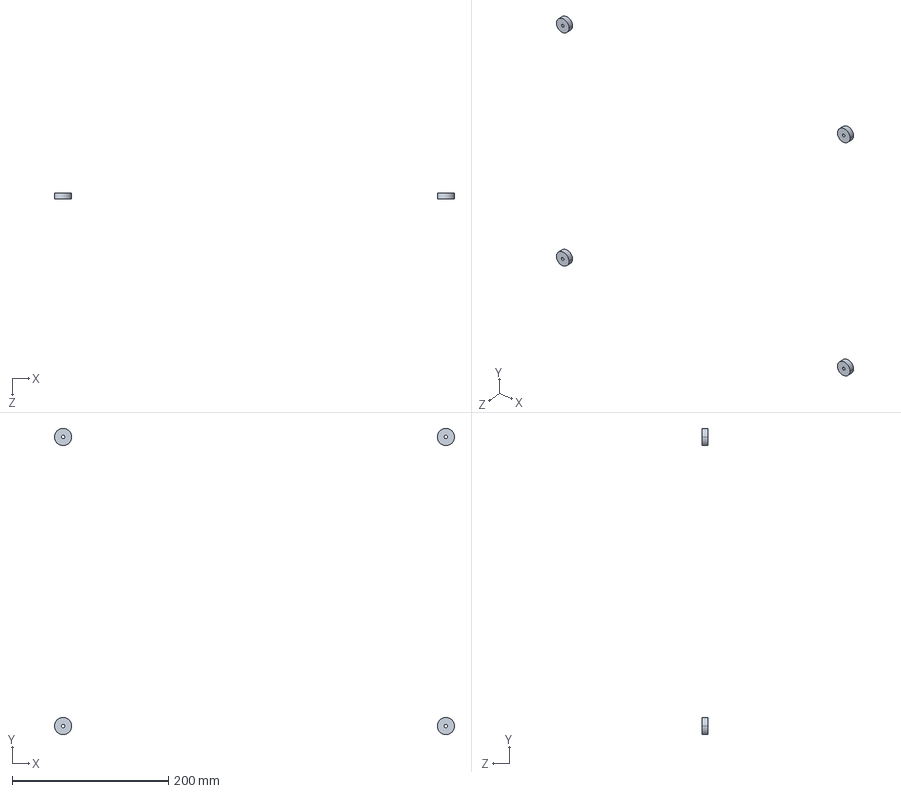
[picture p69: CAD file, 2026-08-29]
exports/BackFeetPack_V11_4xCapturedEPDM.STEP
512.0 x 392.0 x 8.00 mm
