ryule5158/A-Rack-for-Eurorack-Modules/exports/RearKickstandHeel_V11_17_4PH_Keyed.STEP

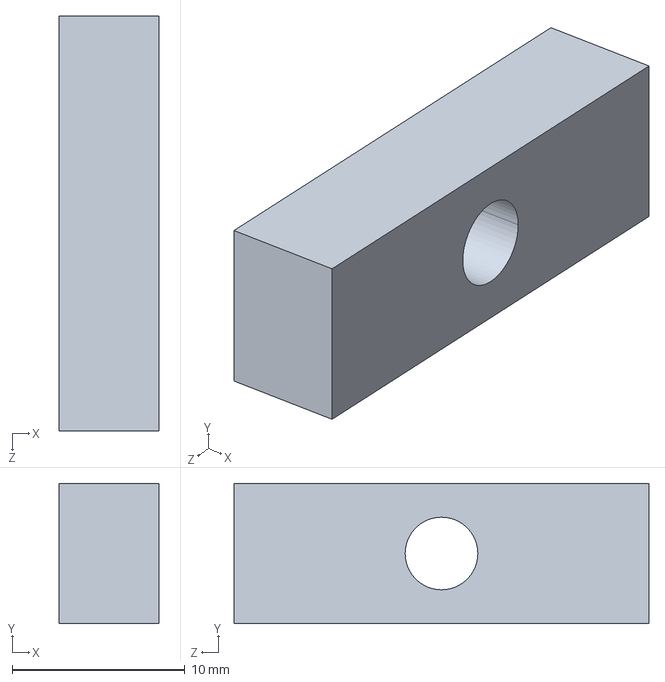
[picture p70: CAD file, 2026-08-29]
exports/RearKickstandHeel_V11_17_4PH_Keyed.STEP
5.80 x 8.10 x 24.0 mm
