ryule5158/A-Rack-for-Eurorack-Modules/exports/RymoviaRail_104HP_V11_AISI304_ThreadStrip.STEP

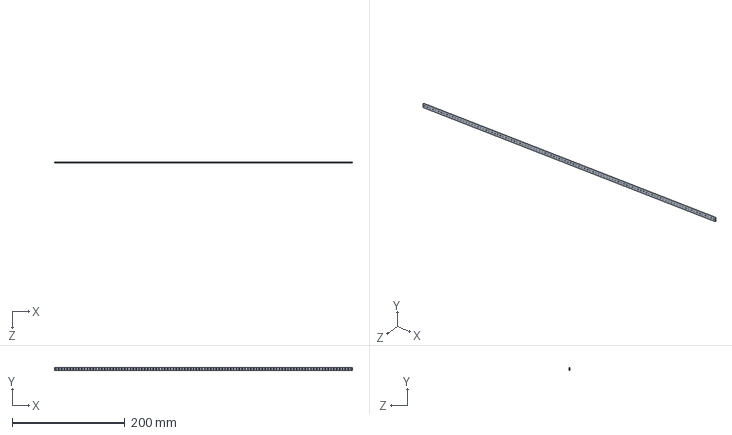
[picture p71: CAD file, 2026-08-29]
exports/RymoviaRail_104HP_V11_AISI304_ThreadStrip.STEP
528.3 x 6.00 x 2.00 mm
