ryule5158/A-Rack-for-Eurorack-Modules/exports/CarryHandle_V11_SouthcoP9_128.STEP

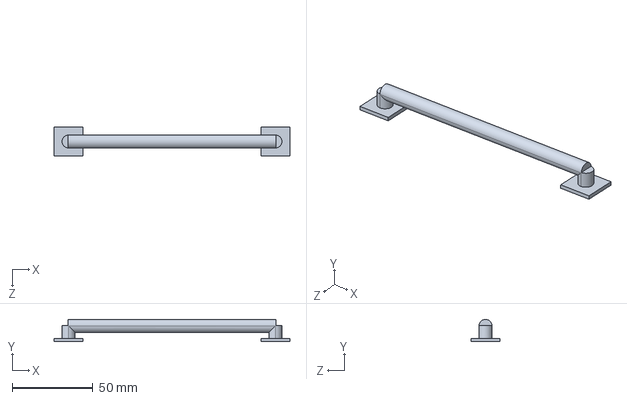
[picture p72: CAD file, 2026-08-29]
exports/CarryHandle_V11_SouthcoP9_128.STEP
146.0 x 13.8 x 18.0 mm
