ryule5158/A-Rack-for-Eurorack-Modules/exports/BackVesaDoubler_V11_5052_Separate.STEP

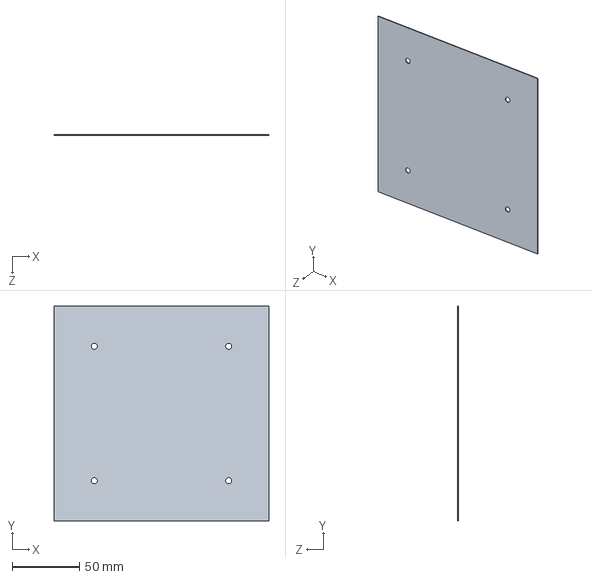
[picture p73: CAD file, 2026-08-29]
exports/BackVesaDoubler_V11_5052_Separate.STEP
160.0 x 160.0 x 0.5 mm
