ryule5158/A-Rack-for-Eurorack-Modules/exports/VesaLoadFrame_V11_OnePiece6061.STEP

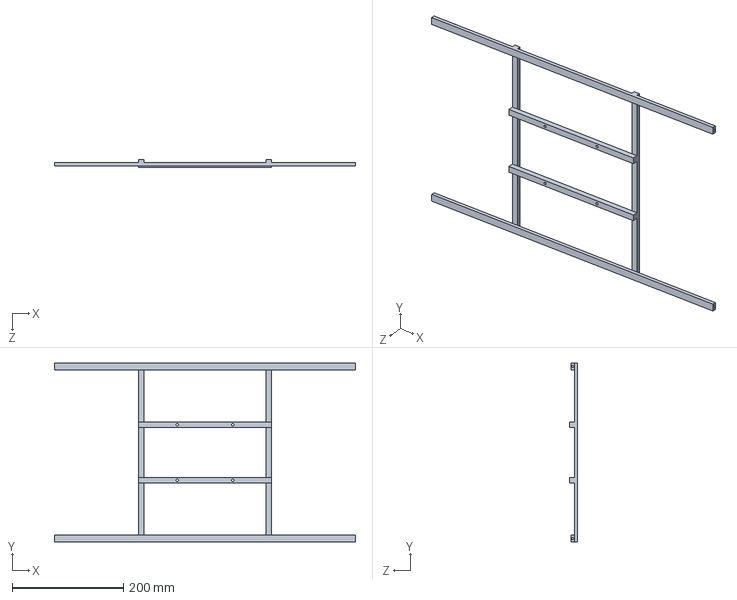
[picture p74: CAD file, 2026-08-29]
exports/VesaLoadFrame_V11_OnePiece6061.STEP
542.0 x 322.0 x 15.0 mm
