ryule5158/A-Rack-for-Eurorack-Modules/exports/ShellCornerFastenerPack_V11_8xM4.STEP

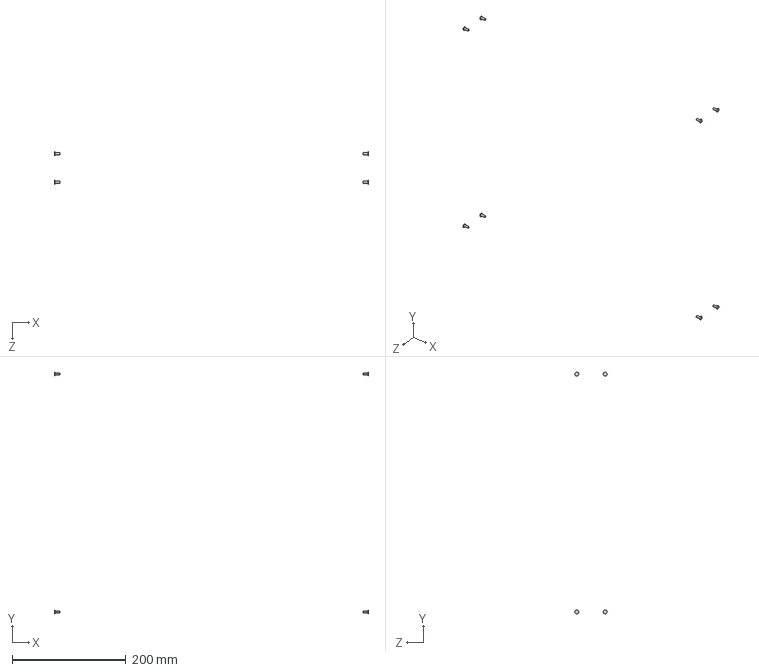
[picture p76: CAD file, 2026-08-29]
exports/ShellCornerFastenerPack_V11_8xM4.STEP
552.0 x 425.2 x 57.2 mm
