ryule5158/A-Rack-for-Eurorack-Modules/exports/FrontAntiTipFoot_V11_OvermouldCaptured.STEP

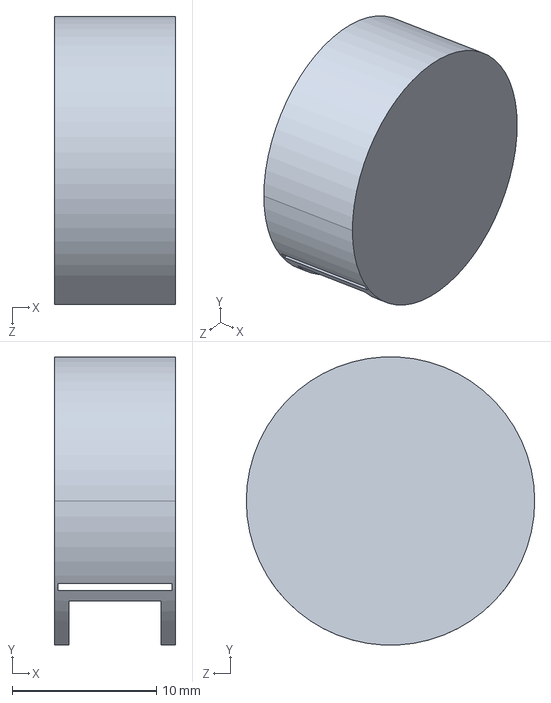
[picture p77: CAD file, 2026-08-29]
exports/FrontAntiTipFoot_V11_OvermouldCaptured.STEP
8.40 x 20.0 x 20.0 mm
