ryule5158/A-Rack-for-Eurorack-Modules/exports/FrontAntiTipBracketFastenerPack_V11_8xM4.STEP

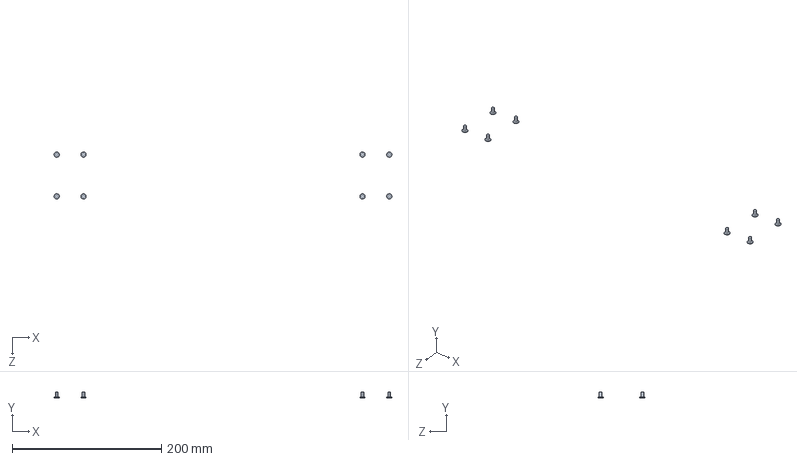
[picture p78: CAD file, 2026-08-29]
exports/FrontAntiTipBracketFastenerPack_V11_8xM4.STEP
453.2 x 7.40 x 63.2 mm
