ryule5158/A-Rack-for-Eurorack-Modules/exports/LidLatchBailPack_V11_ClosedState.STEP

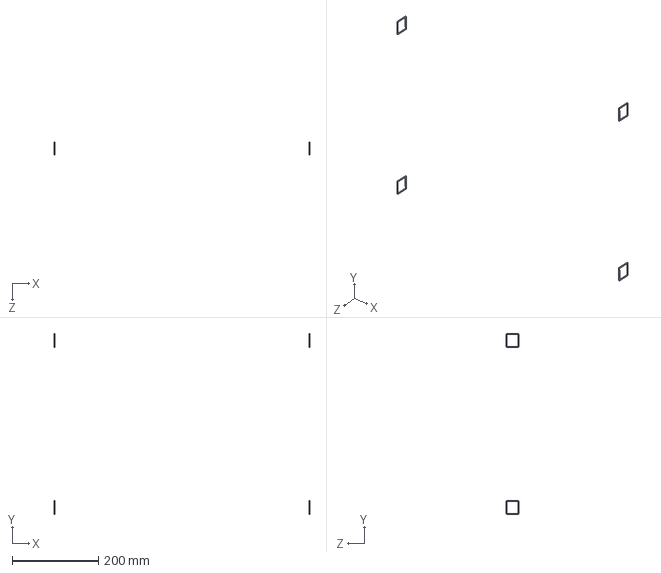
[picture p79: CAD file, 2026-08-29]
exports/LidLatchBailPack_V11_ClosedState.STEP
594.1 x 420.5 x 30.8 mm
