ryule5158/A-Rack-for-Eurorack-Modules/exports/LidLatchBodyPack_V11_SouthcoV7_31x72.STEP

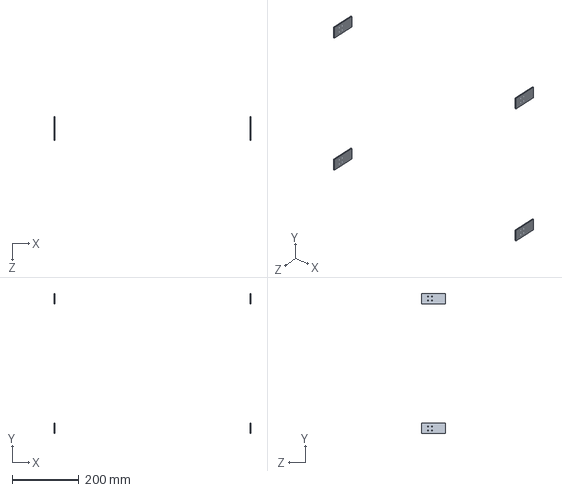
[picture p80: CAD file, 2026-08-29]
exports/LidLatchBodyPack_V11_SouthcoV7_31x72.STEP
589.0 x 419.0 x 72.0 mm
