ryule5158/A-Rack-for-Eurorack-Modules/exports/FrontAntiTipBracketPack_V11_DoubleShear.STEP

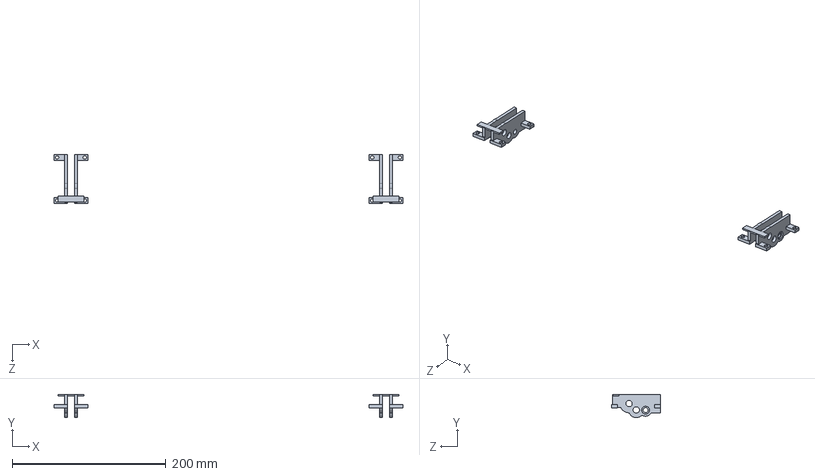
[picture p81: CAD file, 2026-08-29]
exports/FrontAntiTipBracketPack_V11_DoubleShear.STEP
454.0 x 30.3 x 64.0 mm
