ryule5158/A-Rack-for-Eurorack-Modules/exports/LowerEdge_V11_Vented_AntiTipMounts.STEP

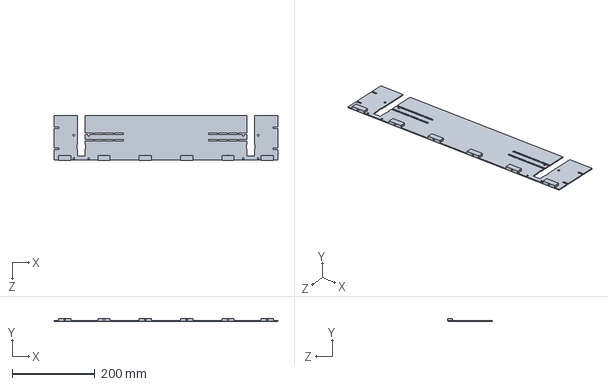
[picture p82: CAD file, 2026-08-29]
exports/LowerEdge_V11_Vented_AntiTipMounts.STEP
542.0 x 7.00 x 108.5 mm
