ryule5158/A-Rack-for-Eurorack-Modules/exports/RearKickstandFoot_V11_OvermouldCaptured.STEP

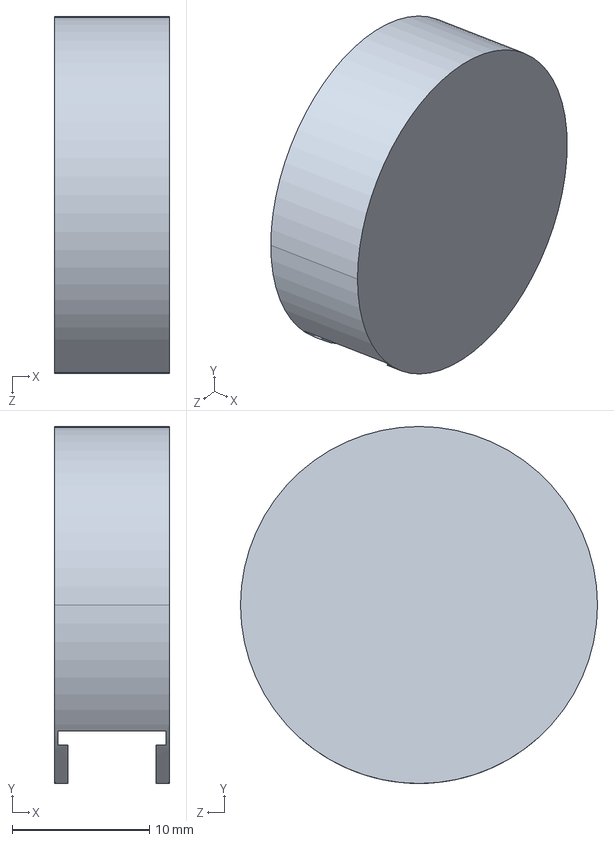
[picture p83: CAD file, 2026-08-29]
exports/RearKickstandFoot_V11_OvermouldCaptured.STEP
8.40 x 26.0 x 26.0 mm
