ryule5158/A-Rack-for-Eurorack-Modules/exports/Rack4Modules_ClearanceCheck_V10_RymoviaPhaseHaloRear.STEP

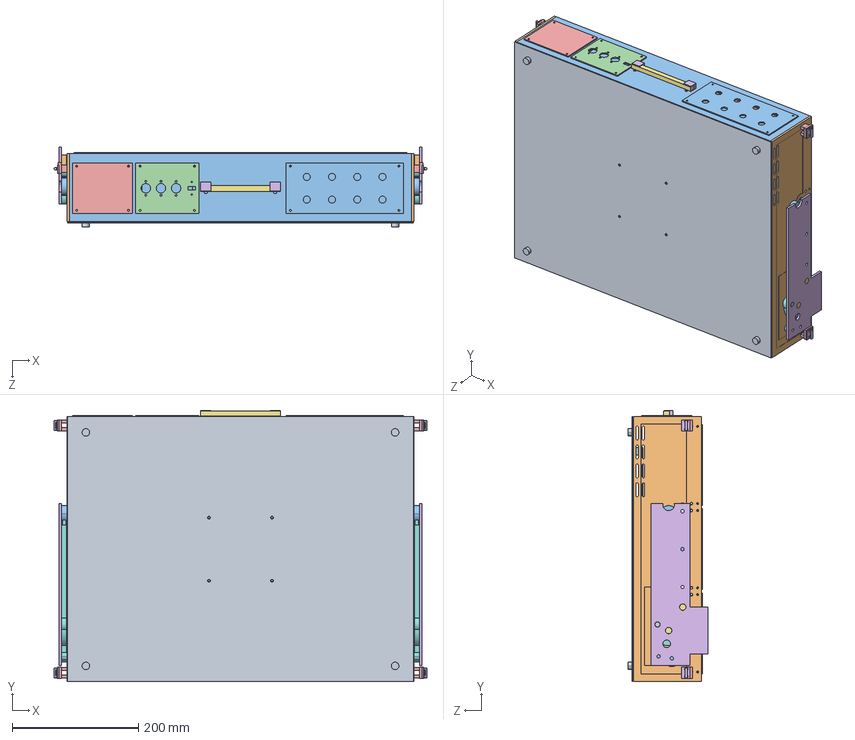
[picture p84: CAD file, 2026-08-26]
exports/Rack4Modules_ClearanceCheck_V10_RymoviaPhaseHaloRear.STEP
591.0 x 430.0 x 126.0 mm
BackPanel_V10_5052_RymoviaPhaseHalo
SideFrame_V09_SecureLidInner x 2
UpperEdge_V04_Adapter_MIDI_Handle_Audio_ClearPower
LowerEdge_V03_HiddenVent
Rail_104HP_V07_ClosedTube_EndBoss x 6
ThreadStrip_104HP_M3_AISI304_V04 x 6
RailEndBlock_M3 x 12
RearCrossBeam_6061 x 2
VesaStile_6061 x 2
VesaBridge_6061_V04_DirectMount x 2
UpperAudio_V04_2x4_TRS635
UpperMidiUsb_V04_3xDIN_USB_C_Inline
UpperAdapterBlank_V04_95mm
RearCarryHandle_V03_ClearanceFit
SideKickstand_V07_185mm_8x28 x 2
FourBackFeet_V03
FitGauge_104HP_3U x 3
ModuleDepthEnvelope_85mm_V03 x 3
ReservedPowerBus_500x85x20
ReservedPowerSupply_210x90x45
KickstandOuterCheek_V07_4mm x 2
KickstandPivotPin_V07_10mm x 2
KickstandSpacer_V07_8p8mm_M5 x 10
KickstandLoadStopPin_V07_10mm x 2
KickstandCaptiveIndexPin_V07_8mm x 2
KickstandHeelInsert_V07 x 2
KickstandFootPad_V07_Rubber x 2
CarryHandleSpreader_V07_6061_4mm
LidLatchCaseBridgePack_V09_6061
LidLatchKeeperPack_V09_Stainless
LidLatchCaseFastenerPack_V09_A4_M3
