ryule5158/A-Rack-for-Eurorack-Modules/exports/BackPanel_V10_5052_RymoviaPhaseHalo.STEP

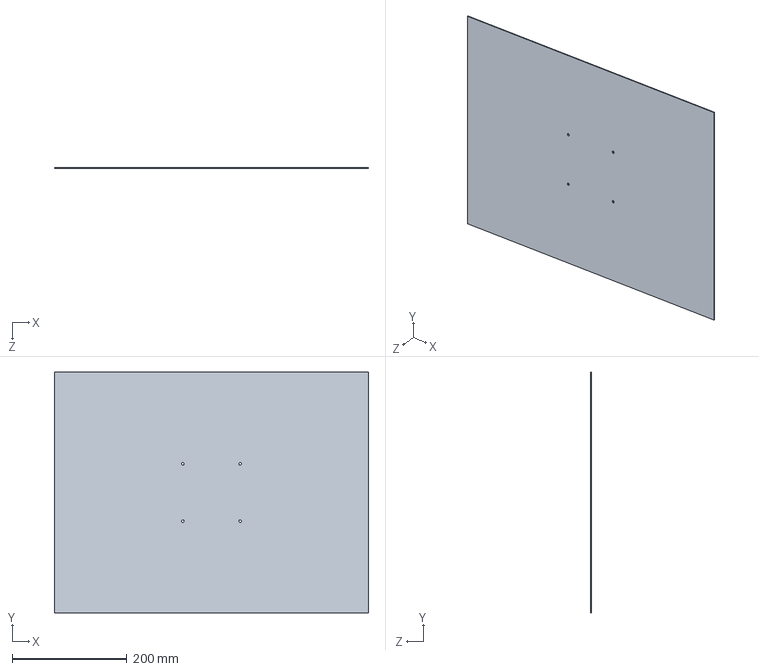
[picture p87: CAD file, 2026-08-26]
exports/BackPanel_V10_5052_RymoviaPhaseHalo.STEP
548.0 x 420.0 x 2.00 mm
