ryule5158/A-Rack-for-Eurorack-Modules/exports/LidLatchKeeperPack_V09_Stainless.STEP

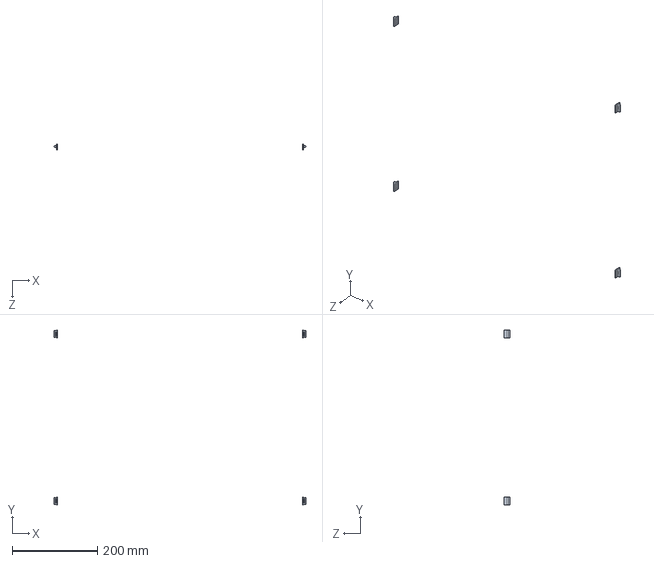
[picture p91: CAD file, 2026-08-26]
exports/LidLatchKeeperPack_V09_Stainless.STEP
591.0 x 410.0 x 14.0 mm
