ryule5158/A-Rack-for-Eurorack-Modules/exports/LidLatchBodyPack_V09_Black.STEP

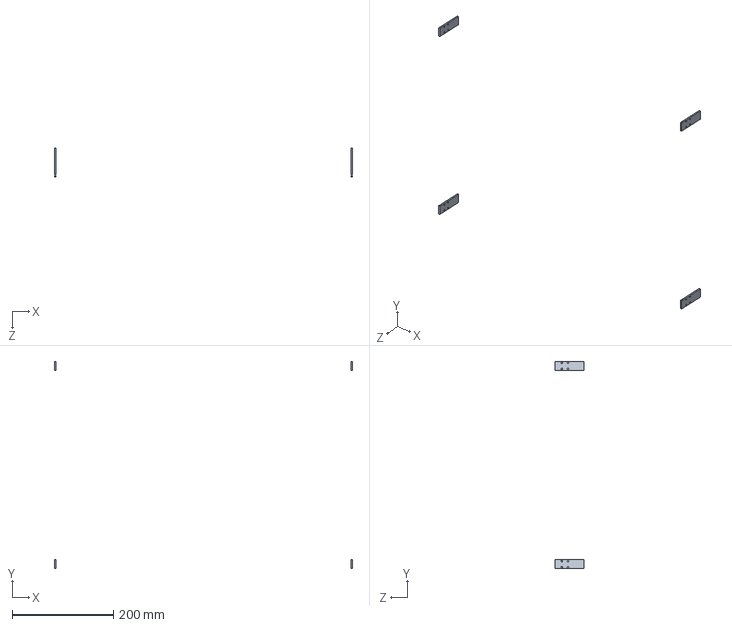
[picture p92: CAD file, 2026-08-26]
exports/LidLatchBodyPack_V09_Black.STEP
589.0 x 410.0 x 58.0 mm
