ryule5158/A-Rack-for-Eurorack-Modules/exports/LidLatchCaseFastenerPack_V09_A4_M3.STEP

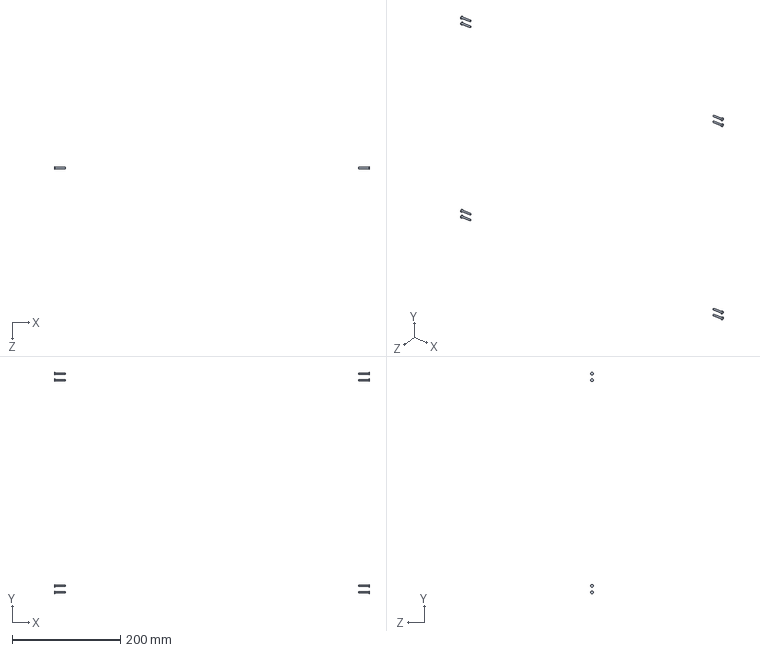
[picture p93: CAD file, 2026-08-26]
exports/LidLatchCaseFastenerPack_V09_A4_M3.STEP
582.0 x 409.5 x 5.50 mm
