ryule5158/A-Rack-for-Eurorack-Modules/exports/LidLatchLockedIndicatorPack_V09_Red.STEP

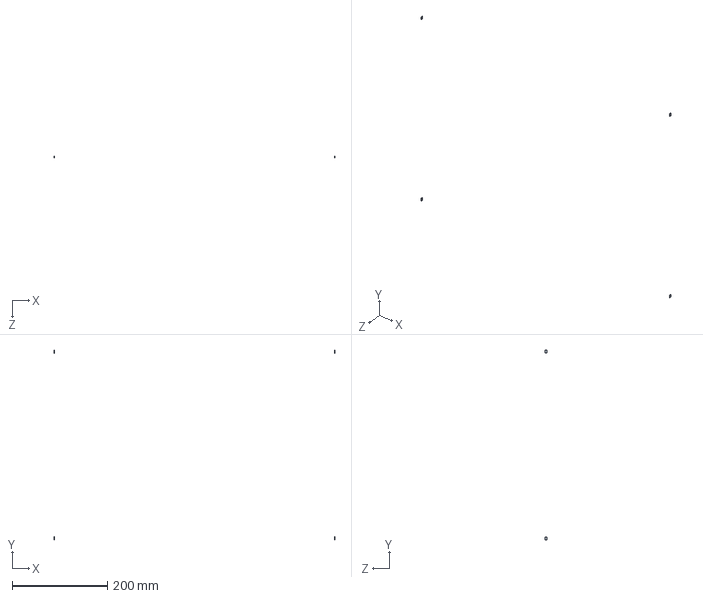
[picture p94: CAD file, 2026-08-26]
exports/LidLatchLockedIndicatorPack_V09_Red.STEP
589.6 x 398.0 x 4.00 mm
