ryule5158/A-Rack-for-Eurorack-Modules/exports/LidLatchDoublerPack_V09_5052.STEP

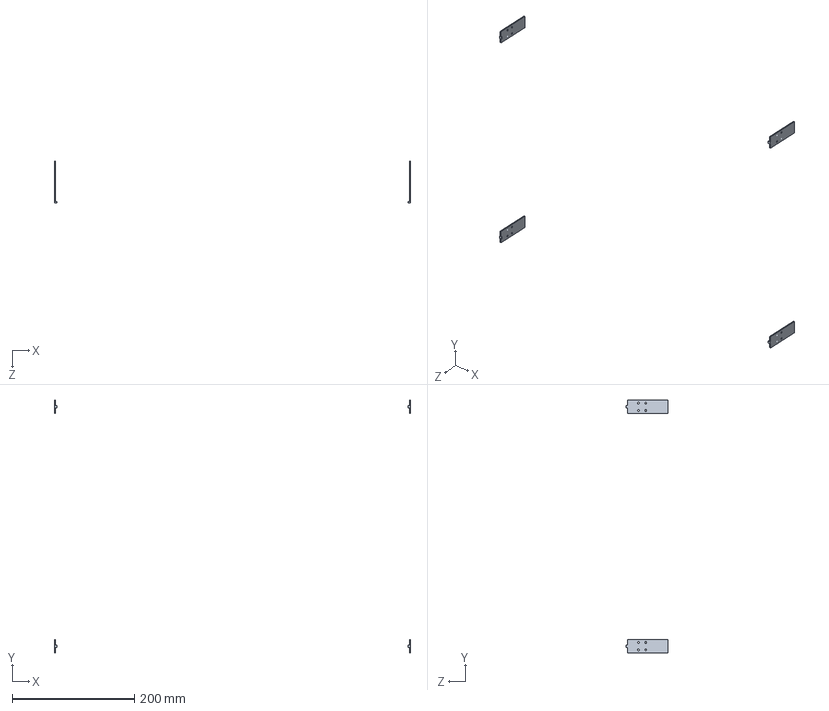
[picture p95: CAD file, 2026-08-26]
exports/LidLatchDoublerPack_V09_5052.STEP
583.0 x 414.0 x 68.0 mm
