ryule5158/A-Rack-for-Eurorack-Modules/exports/LidLatchBailPack_V09_Stainless.STEP

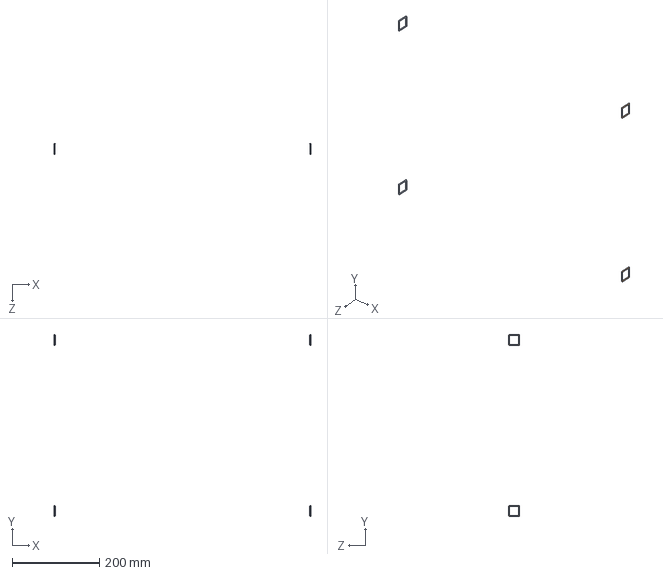
[picture p96: CAD file, 2026-08-26]
exports/LidLatchBailPack_V09_Stainless.STEP
589.5 x 417.5 x 25.8 mm
