ryule5158/A-Rack-for-Eurorack-Modules/exports/LidCompressionPadPack_V09_EPDM.STEP

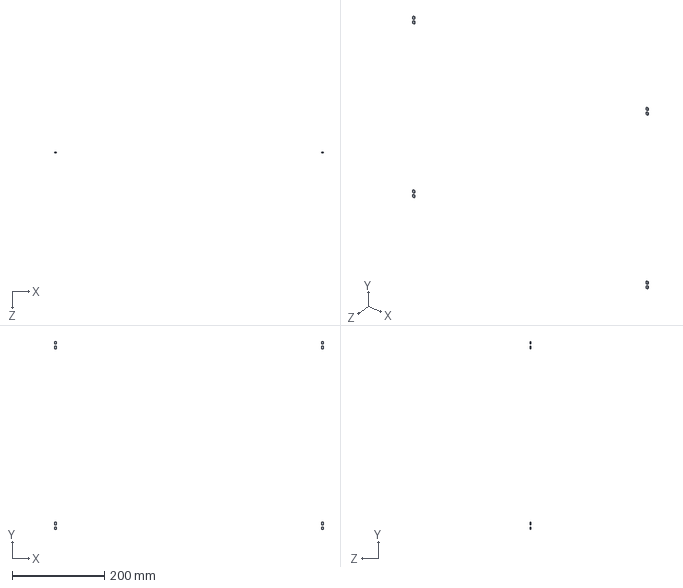
[picture p97: CAD file, 2026-08-26]
exports/LidCompressionPadPack_V09_EPDM.STEP
583.0 x 408.0 x 2.00 mm
