ryule5158/A-Rack-for-Eurorack-Modules/exports/LidLatchCaseBridgePack_V09_6061.STEP

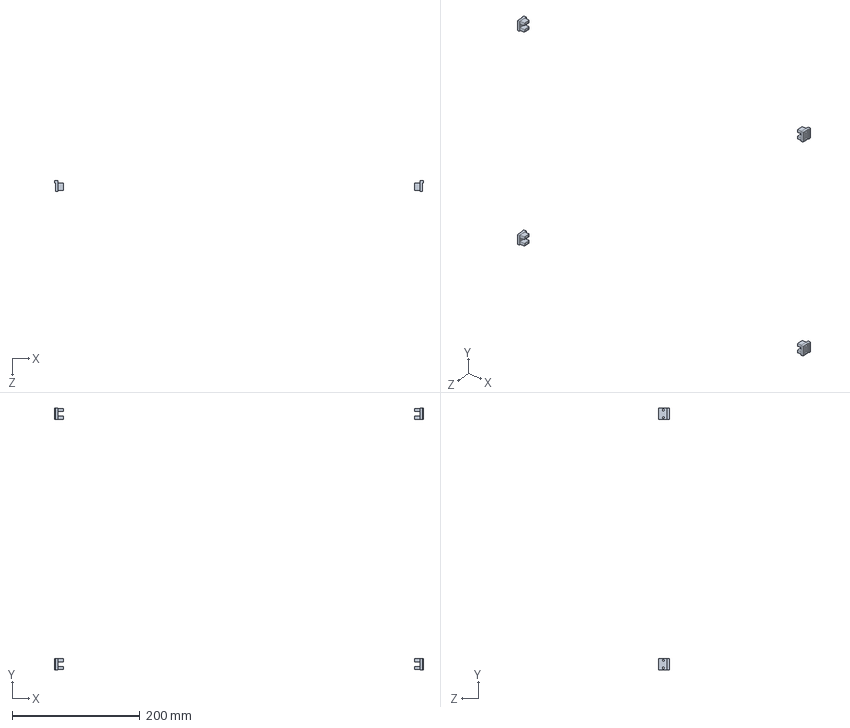
[picture p98: CAD file, 2026-08-26]
exports/LidLatchCaseBridgePack_V09_6061.STEP
578.0 x 410.0 x 18.0 mm
