ryule5158/A-Rack-for-Eurorack-Modules/exports/SideFrame_V09_SecureLidInner.STEP

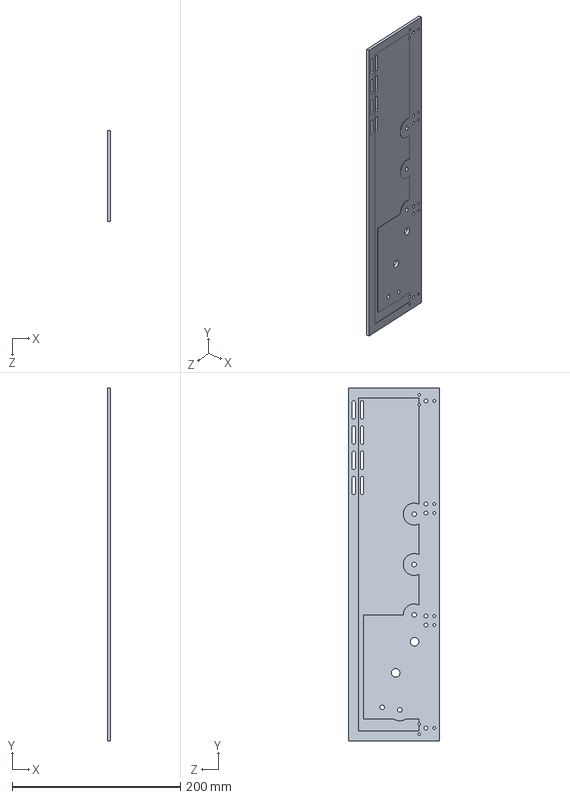
[picture p99: CAD file, 2026-08-26]
exports/SideFrame_V09_SecureLidInner.STEP
4.00 x 420.0 x 108.0 mm
