ryule5158/A-Rack-for-Eurorack-Modules/exports/CarryHandleSpreader_V07_6061_4mm.STEP

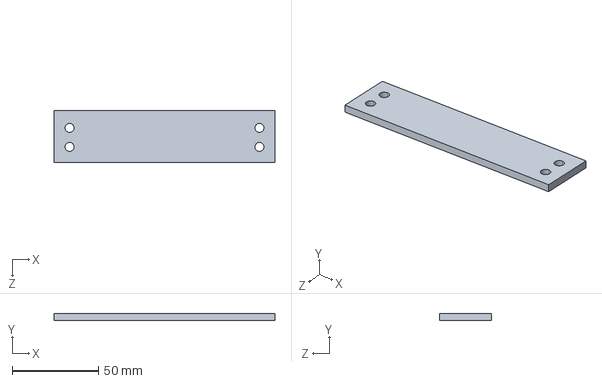
[picture p100: CAD file, 2026-08-26]
exports/CarryHandleSpreader_V07_6061_4mm.STEP
128.0 x 4.00 x 30.0 mm
