ryule5158/A-Rack-for-Eurorack-Modules/exports/KickstandOuterCheek_V07_4mm.STEP

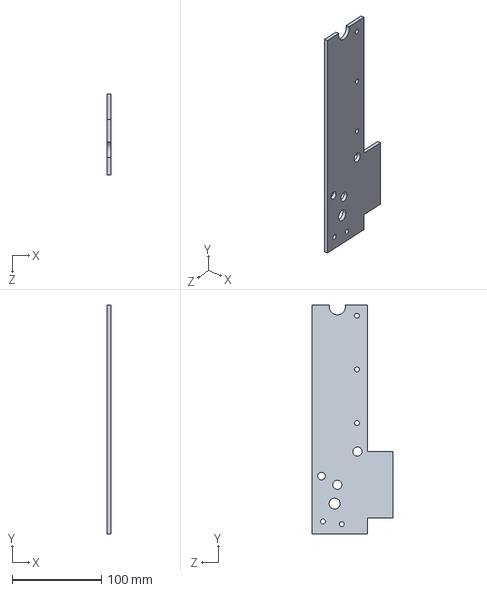
[picture p101: CAD file, 2026-08-26]
exports/KickstandOuterCheek_V07_4mm.STEP
4.00 x 256.0 x 90.0 mm
