ryule5158/A-Rack-for-Eurorack-Modules/exports/Rail_104HP_V07_ClosedTube_EndBoss.STEP

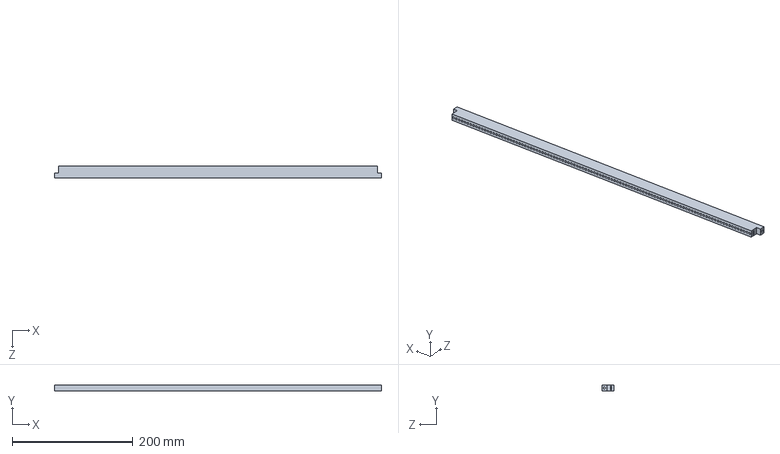
[picture p102: CAD file, 2026-08-26]
exports/Rail_104HP_V07_ClosedTube_EndBoss.STEP
542.0 x 10.0 x 20.0 mm
