ryule5158/A-Rack-for-Eurorack-Modules/exports/SideKickstand_V07_185mm_8x28.STEP

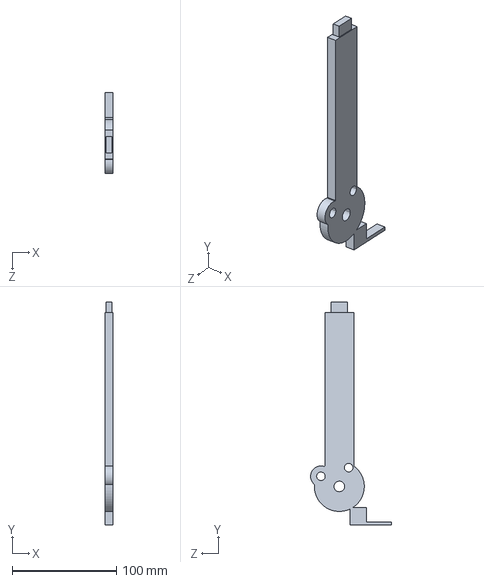
[picture p103: CAD file, 2026-08-26]
exports/SideKickstand_V07_185mm_8x28.STEP
8.00 x 214.0 x 77.6 mm
