ryule5158/A-Rack-for-Eurorack-Modules/exports/KickstandCaptiveIndexPin_V07_8mm.STEP

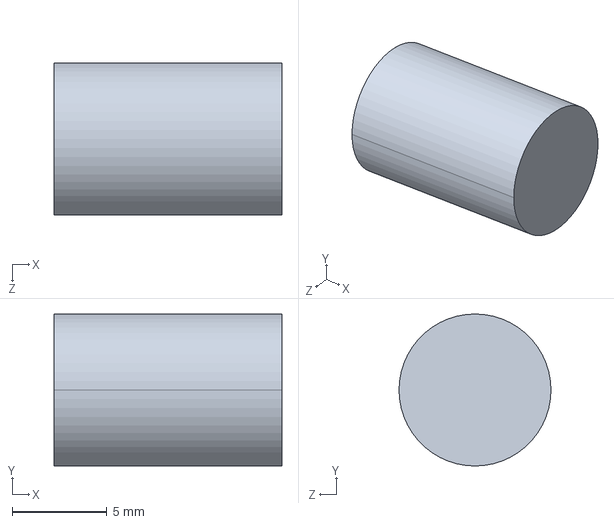
[picture p104: CAD file, 2026-08-26]
exports/KickstandCaptiveIndexPin_V07_8mm.STEP
12.0 x 8.00 x 8.00 mm
