ryule5158/A-Rack-for-Eurorack-Modules/exports/KickstandHeelInsert_V07.STEP

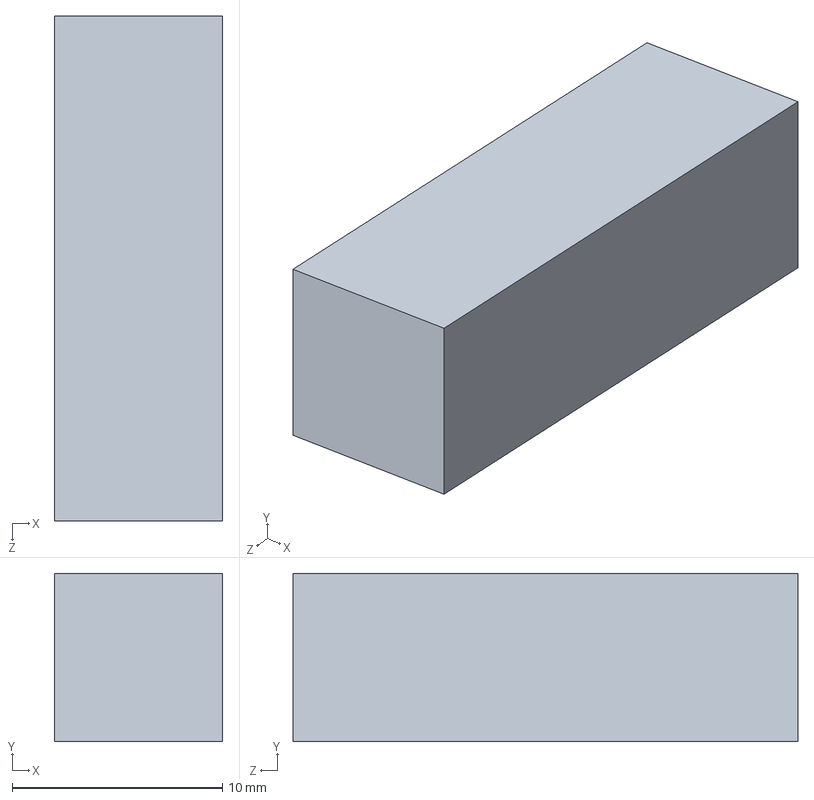
[picture p105: CAD file, 2026-08-26]
exports/KickstandHeelInsert_V07.STEP
8.00 x 8.00 x 24.0 mm
