ryule5158/A-Rack-for-Eurorack-Modules/exports/KickstandPivotPin_V07_10mm.STEP

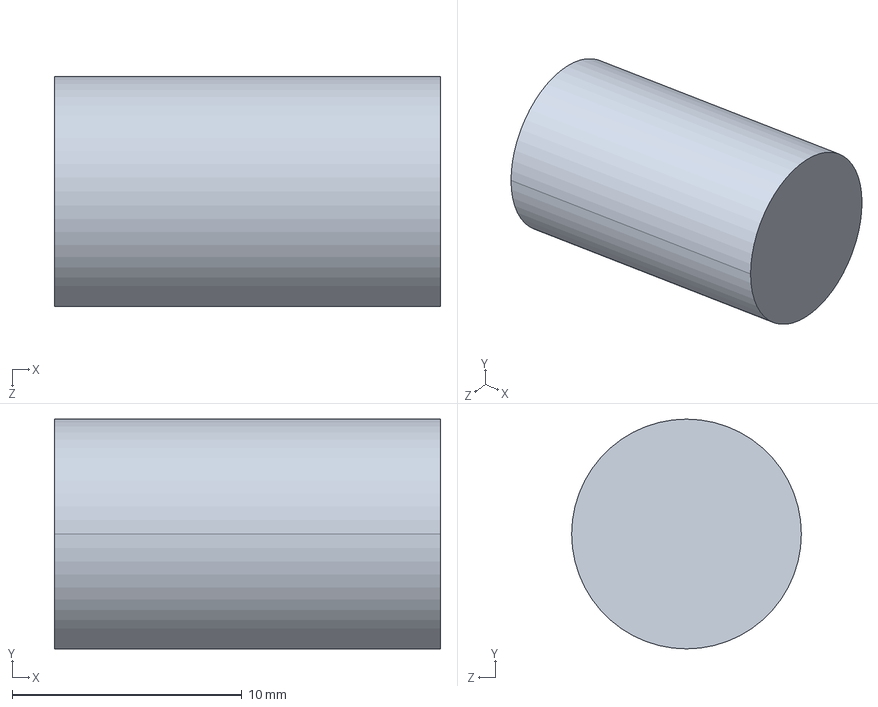
[picture p106: CAD file, 2026-08-26]
exports/KickstandPivotPin_V07_10mm.STEP
16.8 x 10.0 x 10.0 mm
