ryule5158/A-Rack-for-Eurorack-Modules/exports/KickstandFootPad_V07_Rubber.STEP

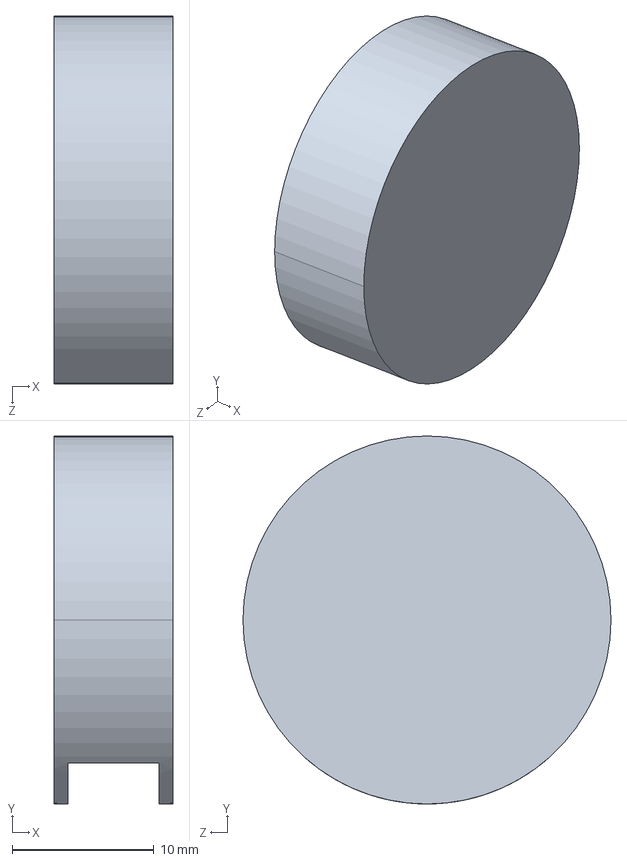
[picture p107: CAD file, 2026-08-26]
exports/KickstandFootPad_V07_Rubber.STEP
8.40 x 26.0 x 26.0 mm
