ryule5158/A-Rack-for-Eurorack-Modules/exports/RearCarryHandle_V03_ClearanceFit.STEP

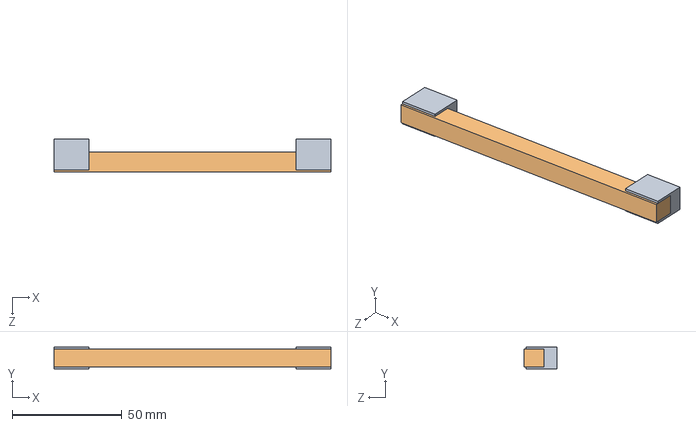
[picture p108: CAD file, 2026-08-26]
exports/RearCarryHandle_V03_ClearanceFit.STEP
126.0 x 10.0 x 15.0 mm
