ryule5158/A-Rack-for-Eurorack-Modules/exports/UpperAudio_V04_2x4_TRS635.STEP

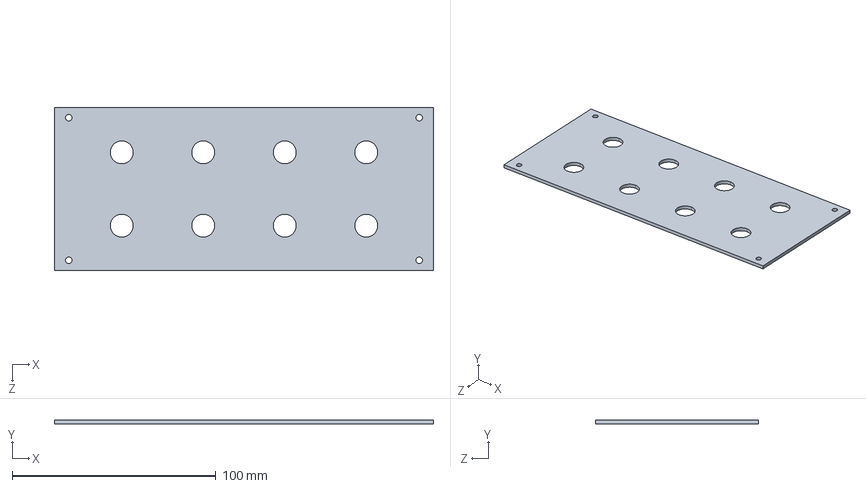
[picture p109: CAD file, 2026-08-26]
exports/UpperAudio_V04_2x4_TRS635.STEP
186.0 x 2.00 x 80.0 mm
