ryule5158/A-Rack-for-Eurorack-Modules/exports/SideKickstand_V04_LowerPivot150mm.STEP

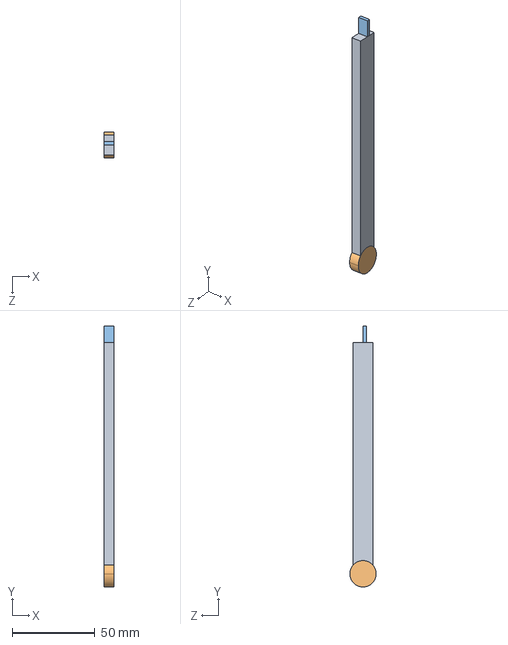
[picture p110: CAD file, 2026-08-26]
exports/SideKickstand_V04_LowerPivot150mm.STEP
6.00 x 158.0 x 16.0 mm
