ryule5158/A-Rack-for-Eurorack-Modules/exports/SideFrame_V04_Vented_DualRailFix.STEP

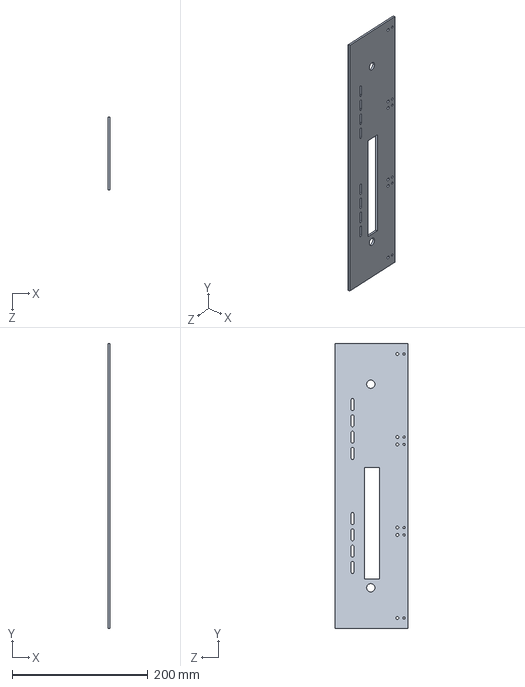
[picture p111: CAD file, 2026-08-26]
exports/SideFrame_V04_Vented_DualRailFix.STEP
3.00 x 420.0 x 108.0 mm
