ryule5158/A-Rack-for-Eurorack-Modules/exports/RearEdgePowerBlank_V03.STEP

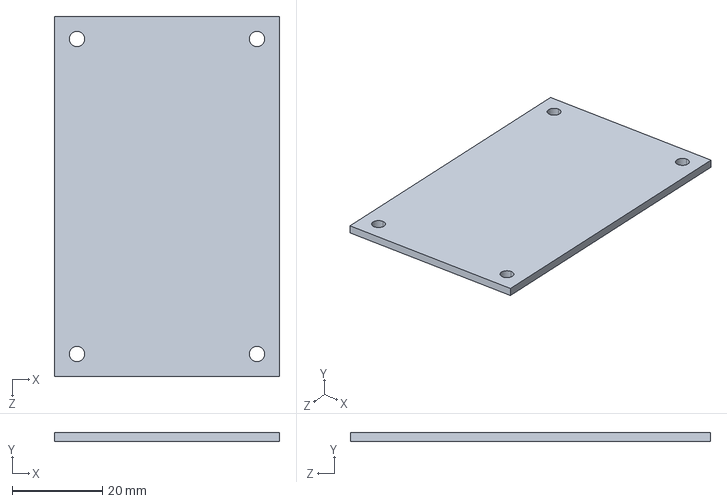
[picture p113: CAD file, 2026-08-26]
exports/RearEdgePowerBlank_V03.STEP
50.0 x 2.00 x 80.0 mm
