ryule5158/A-Rack-for-Eurorack-Modules/exports/Rail_104HP_V04_SpineDualFix.STEP

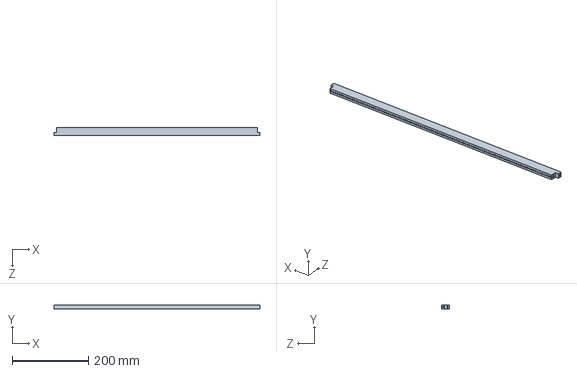
[picture p114: CAD file, 2026-08-26]
exports/Rail_104HP_V04_SpineDualFix.STEP
542.0 x 10.0 x 20.0 mm
