ryule5158/A-Rack-for-Eurorack-Modules/exports/UpperMidiUsb_V04_3xDIN_USB_C_Inline.STEP

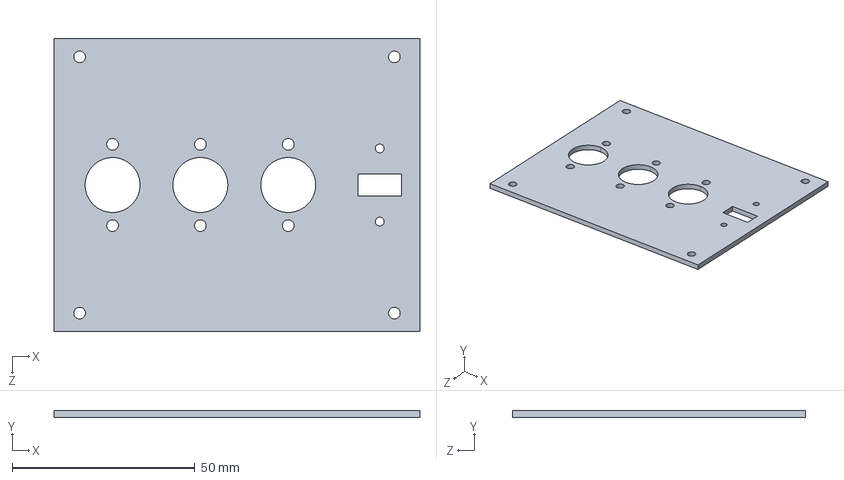
[picture p115: CAD file, 2026-08-26]
exports/UpperMidiUsb_V04_3xDIN_USB_C_Inline.STEP
100.0 x 2.00 x 80.0 mm
