ryule5158/A-Rack-for-Eurorack-Modules/exports/SideKickstand_V05_DoubleShear150mm.STEP

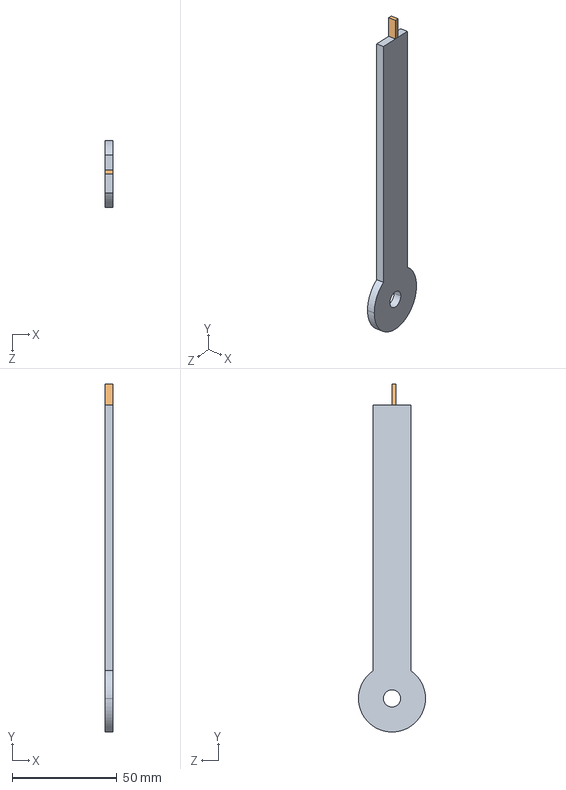
[picture p116: CAD file, 2026-08-26]
exports/SideKickstand_V05_DoubleShear150mm.STEP
4.00 x 166.0 x 32.0 mm
