ryule5158/A-Rack-for-Eurorack-Modules/exports/RearAudio_8xTRS635.STEP

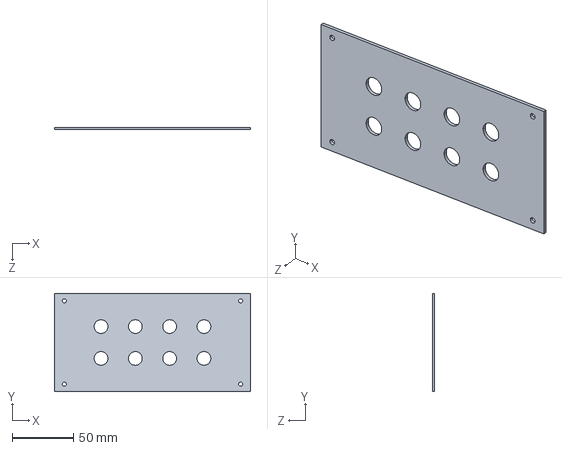
[picture p117: CAD file, 2026-08-26]
exports/RearAudio_8xTRS635.STEP
160.0 x 80.0 x 2.00 mm
