ryule5158/A-Rack-for-Eurorack-Modules/exports/KickstandSpacer_V05_4p8mm.STEP

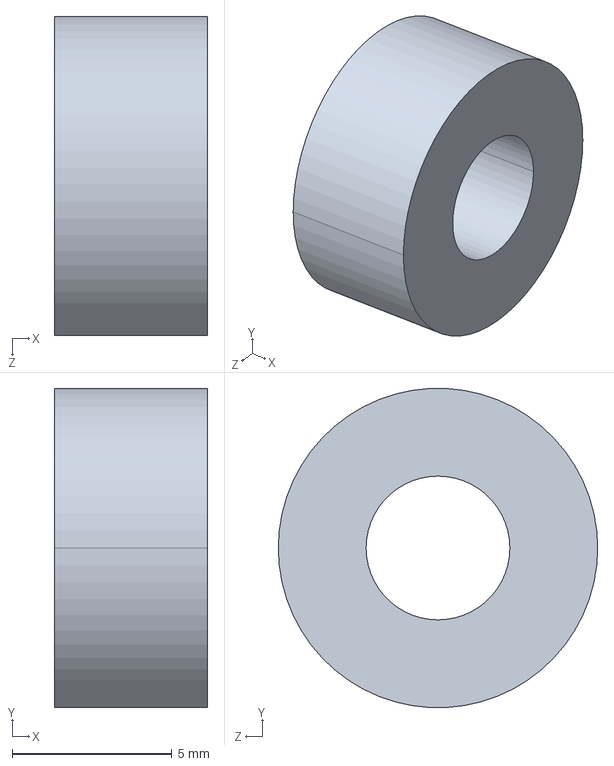
[picture p118: CAD file, 2026-08-26]
exports/KickstandSpacer_V05_4p8mm.STEP
4.80 x 9.99 x 10.0 mm
