ryule5158/A-Rack-for-Eurorack-Modules/exports/KickstandOuterCheek_V05_3mm.STEP

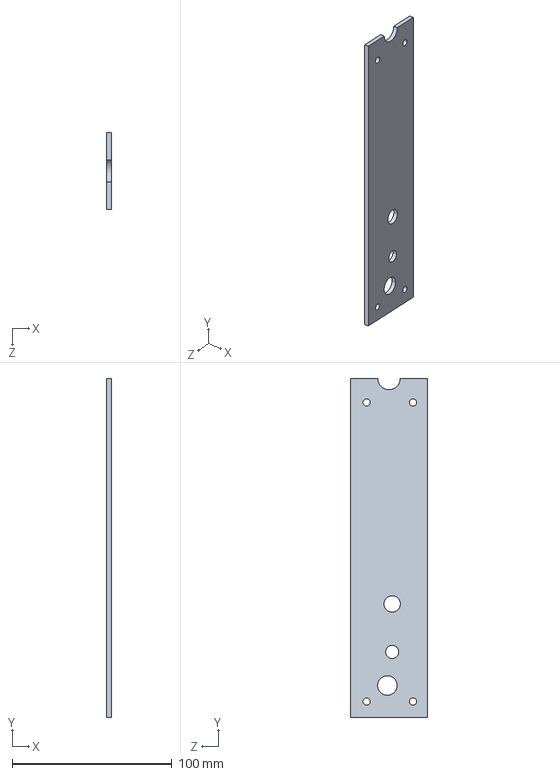
[picture p119: CAD file, 2026-08-26]
exports/KickstandOuterCheek_V05_3mm.STEP
3.00 x 212.0 x 48.0 mm
