ryule5158/A-Rack-for-Eurorack-Modules/cad/assemblies/Rack4Modules_DesktopTilt75_V05.SLDASM

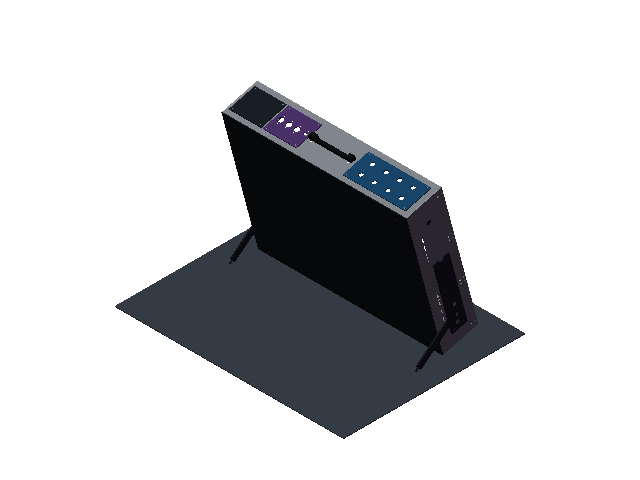
[picture p142: CAD file, 2026-08-26]
cad/assemblies/Rack4Modules_DesktopTilt75_V05.SLDASM
BackPanel_V03_VESAOnly
SideFrame_V05_Vented_DoubleShearInner x 2
UpperEdge_V04_Adapter_MIDI_Handle_Audio_ClearPower
LowerEdge_V03_HiddenVent
Rail_104HP_V04_SpineDualFix x 6
ThreadStrip_104HP_M3_AISI304_V04 x 6
RailEndBlock_M3 x 12
RearCrossBeam_6061 x 2
VesaStile_6061 x 2
VesaBridge_6061_V04_DirectMount x 2
UpperAudio_V04_2x4_TRS635
UpperMidiUsb_V04_3xDIN_USB_C_Inline
UpperAdapterBlank_V04_95mm
RearCarryHandle_V03_ClearanceFit
SideKickstand_V05_DoubleShear150mm x 2
InternalLidCatch_V03 x 4
FourBackFeet_V03
DesktopReferenceSurface_V04
KickstandOuterCheek_V05_3mm x 2
KickstandPivotPin_V05_Flush x 2
KickstandSpacer_V05_4p8mm x 8
KickstandIndexPin_V05_SpringEnvelope x 2
